shadohead/launchlab-mini/firmware/releases/0.6.0-sticks3-qre1113-rotation/README.md

# Initial single-sensor orientation build

Superseded by 0.6.1. The first VQF rotation-only implementation retained RPM/history and disabled estimated travel, but live feedback exposed missing fused post-roll coverage and a display that erased starting inclination. See `manifest.json`. This is a development checkpoint, not an accepted motion release.
