shadohead/launchlab-mini/firmware/releases/0.6.2-sticks3-qre1113-rotation/source/README.md

# LaunchLab Mini for M5StickS3

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

The current single-sensor orientation recap is saved as
[0.6.2-sticks3-qre1113-rotation](../releases/0.6.2-sticks3-qre1113-rotation/README.md).
The former [estimated-travel recap](../releases/0.5.1-sticks3-qre1113-front/README.md) is preserved.
The prior [cube recap](../releases/0.5.0-sticks3-qre1113-cube/README.md) is preserved.
The prior [frozen level recap](../releases/0.4.3-sticks3-qre1113-recap/README.md) is preserved.
The prior [motion/recreate update](../releases/0.4.2-sticks3-qre1113-feedback/README.md) is preserved.
The prior [power update](../releases/0.3.1-sticks3-qre1113-power/README.md) is preserved.
Version `0.6.2-sticks3-rotation`, for StickS3 K150 (ESP32-S3,
8 MB flash, 8 MB OPI PSRAM). Uses the installed Arduino ESP32 3.3.0,
M5Unified 0.2.23 and M5GFX 0.2.30 dependencies. This is a separate board
application; the Waveshare binary cannot be installed on the M5.

## Acquisition and performance

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

## M5 sensor profile

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

## Wiring and controls

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

## Launch motion and recreate practice

Every accepted pull opens five seconds of feedback: RPM, a fixed-center
launcher rotating in an isometric cube, and frozen Start/End tilt circles.
The launcher stays in one location. There is no travel trail, height estimate,
velocity, displacement, or compass heading. Cube and body size are constant
across captures and have no physical distance units. The replay includes the
recorded 500 ms before and 250 ms after the optical pull, runs once over 1.4
seconds, and holds the last pose. The replay preserves measured gravity-relative tilt. Only arbitrary heading is
reset at optical onset; it does not flatten the initial pose.
The circles record gravity-relative tilt at optical onset/end; they never follow
the current sensor. Recap omits numeric angles and is labeled "Rotation only". The thin portrait
rectangle depicts the sensor board; its white short-edge mark is the USB-C end.
Its neutral heading faces the viewer midway between the two front cube walls,
aligned with the nearest vertical edge, instead of following the left wall.
This fixed 45-degree display-heading offset does not change measured tilt,
relative rotation, or Start/End dots. The rectangle remains centered in the cube.
An unknown board-to-launcher mounting rotation is not silently assumed calibrated.
A recalls the recap; B opens history. RPM acquisition is always enabled.

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

The single IMU owner runs at priority 2 on core 0, below the priority-3 ADC
owner. It shares an I2C mutex with M5 button/power operations and never owns the
ADC. `ORIENTATION_STATUS` reports readiness, bias/uncertainty, rest detection,
resets, update count, and worst fusion duration. Every gap over 35 ms resets
orientation while retaining learned gyro bias; captures overlapping gaps are
rejected. The filter settles for 1.5 seconds after startup/reset. There is no
per-launch hold-still requirement. Naturally occurring rest improves bias.
Clipping near 8 g / 2000 deg/s, missing coverage and optical bursts over 2.5
seconds also make motion unavailable. RPM/history still record independently.
Capture waits for fused-sample post-roll coverage, not the newer raw-poll
timestamp. Saving history waits for the motion post-roll; guarded flash writes can cause
IMU gaps outside the finished capture. Failed saves retain prior durable data.

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

## Practice history

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

## Build and validation

```sh
bash firmware/setup-m5.sh
bash firmware/build-m5.sh
clang++ -std=c++17 -O2 -Ifirmware/LaunchLabRpm firmware/tests/test_sticks3.cpp -o /tmp/test-sticks3
/tmp/test-sticks3
clang++ -std=c++17 -O2 firmware/tests/test_sticks3_level.cpp -o /tmp/test-sticks3-level
/tmp/test-sticks3-level
clang++ -std=c++17 -O1 -g -fsanitize=address,undefined firmware/tests/test_sticks3_power.cpp -o /tmp/test-sticks3-power
/tmp/test-sticks3-power
clang++ -std=c++17 -O1 -g -fsanitize=address,undefined firmware/tests/test_launch_feedback.cpp -o /tmp/test-launch-feedback
/tmp/test-launch-feedback
clang++ -std=c++17 -O1 -g -DVQF_SINGLE_PRECISION -fsanitize=address,undefined firmware/tests/test_orientation_estimator.cpp firmware/LaunchLabMini/src/vqf/vqf.cpp -o /tmp/test-orientation
/tmp/test-orientation
clang++ -std=c++17 -O1 -g -fsanitize=address,undefined firmware/tests/test_motion_replay.cpp -o /tmp/test-motion-replay
/tmp/test-motion-replay
clang++ -std=c++17 -O1 -g -fsanitize=address,undefined firmware/tests/test_launch_motion.cpp -o /tmp/test-launch-motion
/tmp/test-launch-motion
clang++ -std=c++17 -O1 -g -fsanitize=address,undefined -Ifirmware/tests/fakes firmware/tests/test_motion_store.cpp -o /tmp/test-motion-store
/tmp/test-motion-store
clang++ -std=c++17 -O2 -Ifirmware/LaunchLabRpm firmware/tests/replay_sticks3.cpp -o /tmp/replay-sticks3
python3 firmware/tests/check_sticks3_replays.py /tmp/replay-sticks3
clang++ -std=c++17 -O1 -g -fsanitize=address,undefined -Ifirmware/LaunchLabRpm firmware/tests/test_practice_history.cpp -o /tmp/test-practice-history
/tmp/test-practice-history
clang++ -std=c++17 -O1 -g -fsanitize=address,undefined -Ifirmware/tests/fakes firmware/tests/test_practice_store.cpp -o /tmp/test-practice-store
/tmp/test-practice-store
```

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
