shadohead/launchlab-mini/firmware/releases/0.7.0-sticks3-qre1113-singlepeak/source/README.md

# LaunchLab Mini for M5StickS3

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

The current single-sensor orientation recap is saved as
[0.7.0-sticks3-qre1113-singlepeak](../releases/0.7.0-sticks3-qre1113-singlepeak/README.md).
The former [estimated-travel recap](../releases/0.5.1-sticks3-qre1113-front/README.md) is preserved.
The prior [cube recap](../releases/0.5.0-sticks3-qre1113-cube/README.md) is preserved.
The prior [frozen level recap](../releases/0.4.3-sticks3-qre1113-recap/README.md) is preserved.
The prior [motion/recreate update](../releases/0.4.2-sticks3-qre1113-feedback/README.md) is preserved.
The prior [power update](../releases/0.3.1-sticks3-qre1113-power/README.md) is preserved.
Version `0.7.0-sticks3-singlepeak`, for StickS3 K150 (ESP32-S3,
8 MB flash, 8 MB OPI PSRAM). Uses the installed Arduino ESP32 3.3.0,
M5Unified 0.2.23 and M5GFX 0.2.30 dependencies. This is a separate board
application; the Waveshare binary cannot be installed on the M5.

## Acquisition and performance

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

## M5 sensor profile

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

One cycle/revolution, the 1,000-RPM start floor, three consistent revolutions
to confirm a pull, first-burst selection and quiet/rewind rearm remain.
Once a pull is confirmed, **one complete valid revolution can set its peak**.
There is no speed-jump veto or requirement to repeat that faster speed.
Its timing, high/low widths, duty, amplitude and uninterrupted neighboring
mark must agree with established optical shape. The arrival mark is checked
after the 0.5-ms optical mean settles; an oversized mark can otherwise cross
the threshold early and create an artificial short period. This delay needs
no additional full revolution. Sustained three-turn speed continues to govern
slowdown detection, so a brief peak does not end an ongoing pull early.
The shared detector defaults retain the former three-turn peak rule; this
single-turn option is enabled by the current M5 profile only.

The existing timing ceiling is 30,000 RPM (2-ms periods), a measurement bound,
not a scientifically established human limit. Detector edge timestamps have
100-us resolution; a single-turn peak is more sensitive to quantization and
optical jitter than the former average. It remains an average over one turn,
not instantaneous speed within that turn or directly measured release RPM.
`RPM_PEAK_MODE` reports the retained three-turn speed and accepted/rejected
single-peak update counters for diagnosis. No magnetometer/IMU speed estimate
is substituted for optical speed.

The M5 profile reproduces one provisional ~5,128 RPM single-turn result
(~4,945 RPM three-turn speed) in the saved pull and rejects the available
weak idle/handling negatives. Old history retains its original three-turn
values; new records use the single-turn metric. Start a fresh practice session
when switching metrics rather than mixing their averages. It remains an initial
measured profile, not proof of repeatable mounted detection or absolute RPM
accuracy. A different sensor, distance or reflective mark may need a different
profile. Do not remove the amplitude floor or notch 60 Hz: 60 Hz is also a
legitimate 3,600 RPM optical signal.

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

## Wiring and controls

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

## Launch motion and recreate practice

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

## Practice history

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

## Build and validation

```sh
bash firmware/setup-m5.sh
bash firmware/build-m5.sh
clang++ -std=c++17 -O2 -Ifirmware/LaunchLabRpm firmware/tests/test_sticks3.cpp -o /tmp/test-sticks3
/tmp/test-sticks3
clang++ -std=c++17 -O2 firmware/tests/test_sticks3_level.cpp -o /tmp/test-sticks3-level
/tmp/test-sticks3-level
clang++ -std=c++17 -O1 -g -fsanitize=address,undefined firmware/tests/test_sticks3_power.cpp -o /tmp/test-sticks3-power
/tmp/test-sticks3-power
clang++ -std=c++17 -O1 -g -fsanitize=address,undefined firmware/tests/test_launch_feedback.cpp -o /tmp/test-launch-feedback
/tmp/test-launch-feedback
clang++ -std=c++17 -O1 -g -DVQF_SINGLE_PRECISION -fsanitize=address,undefined firmware/tests/test_orientation_estimator.cpp firmware/LaunchLabMini/src/vqf/vqf.cpp -o /tmp/test-orientation
/tmp/test-orientation
clang++ -std=c++17 -O1 -g -fsanitize=address,undefined firmware/tests/test_motion_replay.cpp -o /tmp/test-motion-replay
/tmp/test-motion-replay
clang++ -std=c++17 -O1 -g -fsanitize=address,undefined firmware/tests/test_launch_motion.cpp -o /tmp/test-launch-motion
/tmp/test-launch-motion
clang++ -std=c++17 -O1 -g -fsanitize=address,undefined -Ifirmware/tests/fakes firmware/tests/test_motion_store.cpp -o /tmp/test-motion-store
/tmp/test-motion-store
clang++ -std=c++17 -O2 -Ifirmware/LaunchLabRpm firmware/tests/replay_sticks3.cpp -o /tmp/replay-sticks3
python3 firmware/tests/check_sticks3_replays.py /tmp/replay-sticks3
clang++ -std=c++17 -O1 -g -fsanitize=address,undefined -Ifirmware/LaunchLabRpm firmware/tests/test_practice_history.cpp -o /tmp/test-practice-history
/tmp/test-practice-history
clang++ -std=c++17 -O1 -g -fsanitize=address,undefined -Ifirmware/tests/fakes firmware/tests/test_practice_store.cpp -o /tmp/test-practice-store
/tmp/test-practice-store
```

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
