shadohead/launchlab-mini/firmware/releases/0.3.0-sticks3-qre1113/source/LaunchLabMini/README.md

# Saved QRE1113 Arduino source

This is the self-contained executable source for runtime
`0.3.0-sticks3-practice`, saved as the working M5StickS3 K150 + SparkFun QRE1113
analog package. The sketch and headers match the installed build's source.
See the [package README](../../README.md) for wiring, controls, restoration
and validation, and the [current target documentation](../../../../LaunchLabMini/README.md)
for acquisition and build details.
