shadohead/launchlab-mini/firmware/releases/0.3.1-sticks3-qre1113-power/source/LaunchLabMini/README.md

# Saved Arduino sketch

This is the exact compiled source for runtime `0.3.1-sticks3-power`, saved as
`0.3.1-sticks3-qre1113-power`. See the [release README](../../README.md) for
wiring, controls, restoration and validation.
