shadohead/launchlab-mini/firmware/releases/0.4.3-sticks3-qre1113-recap/source/LaunchLabMini/README.md

# LaunchLab Mini for M5StickS3

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

The current recap update is saved as
[0.4.3-sticks3-qre1113-recap](../releases/0.4.3-sticks3-qre1113-recap/README.md).
The prior [motion/recreate update](../releases/0.4.2-sticks3-qre1113-feedback/README.md) is preserved.
The prior [power update](../releases/0.3.1-sticks3-qre1113-power/README.md) is preserved.
Version `0.4.3-sticks3-recap`, for StickS3 K150 (ESP32-S3,
8 MB flash, 8 MB OPI PSRAM). Uses the installed Arduino ESP32 3.3.0,
M5Unified 0.2.23 and M5GFX 0.2.30 dependencies. This is a separate board
application; the Waveshare binary cannot be installed on the M5.

## Acquisition and performance

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

## M5 sensor profile

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

## Wiring and controls

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

## Launch motion and recreate practice

Every new accepted pull opens five seconds of feedback on the main page,
showing RPM, the same relative turn path, and two frozen circle/dot indicators:
Start on the left and End on the right. These estimate the recorded tilt at
optical burst onset and end, using the pre-launch acceleration baseline and
full-rate gyro integration before the chart is reduced to 48 points. They do
not follow the current live level. The recap omits numeric angles, end rotation
text and the path scale label. Travel height and distance are not estimated.
After capture finishes, the full five-second display starts, then
returns to live automatically. A tap on A recalls the latest launch for another
five seconds; tapping A again returns immediately. Measurement remains enabled
in both views. A newer pull replaces the feedback and restarts the timer.
After reboot, A can show the latest saved RPM; its motion is available only
when that same pull was the saved reference. Otherwise the graph and circles
remain empty until a fresh pull. The most recent in-memory trace is kept after the
five-second display ends. B still opens the history and practice pages.

Tap B from live, then A through the tabs to Motion or Recreate. There is no
hold-still requirement; capture runs during normal handling and pulls. Motion draws the launcher's relative tilt
path in degrees. The first usable pull in Recreate becomes the reference;
subsequent pulls compare against it. Hold A to select the latest usable pull,
or hold B to use the next usable pull as a new reference. The reference is
saved across reboot in separate alternating checksummed `ll-motion` NVS slots.
Schema 3 stores both frozen tilt snapshots and the automatic stationary-bias
flag in the existing 1124-byte image. Schema-1 and schema-2 references remain
readable; their start/end tilt is reconstructed from their recorded gyro and
baseline data.
No historical motion is invented for earlier RPM-only records. The latest
attempt stays in RAM; this version retains one reference, not every motion trace.

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

## Practice history

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

## Build and validation

```sh
bash firmware/setup-m5.sh
bash firmware/build-m5.sh
clang++ -std=c++17 -O2 -Ifirmware/LaunchLabRpm firmware/tests/test_sticks3.cpp -o /tmp/test-sticks3
/tmp/test-sticks3
clang++ -std=c++17 -O2 firmware/tests/test_sticks3_level.cpp -o /tmp/test-sticks3-level
/tmp/test-sticks3-level
clang++ -std=c++17 -O1 -g -fsanitize=address,undefined firmware/tests/test_sticks3_power.cpp -o /tmp/test-sticks3-power
/tmp/test-sticks3-power
clang++ -std=c++17 -O1 -g -fsanitize=address,undefined firmware/tests/test_launch_feedback.cpp -o /tmp/test-launch-feedback
/tmp/test-launch-feedback
clang++ -std=c++17 -O1 -g -fsanitize=address,undefined firmware/tests/test_launch_motion.cpp -o /tmp/test-launch-motion
/tmp/test-launch-motion
clang++ -std=c++17 -O1 -g -fsanitize=address,undefined -Ifirmware/tests/fakes firmware/tests/test_motion_store.cpp -o /tmp/test-motion-store
/tmp/test-motion-store
clang++ -std=c++17 -O2 -Ifirmware/LaunchLabRpm firmware/tests/replay_sticks3.cpp -o /tmp/replay-sticks3
python3 firmware/tests/check_sticks3_replays.py /tmp/replay-sticks3
clang++ -std=c++17 -O1 -g -fsanitize=address,undefined -Ifirmware/LaunchLabRpm firmware/tests/test_practice_history.cpp -o /tmp/test-practice-history
/tmp/test-practice-history
clang++ -std=c++17 -O1 -g -fsanitize=address,undefined -Ifirmware/tests/fakes firmware/tests/test_practice_store.cpp -o /tmp/test-practice-store
/tmp/test-practice-store
```

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
