shadohead/launchlab-mini/firmware/releases/0.5.0-sticks3-qre1113-cube/source/LaunchLabMini/README.md

# LaunchLab Mini for M5StickS3

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

The current 3D cube recap is saved as
[0.5.0-sticks3-qre1113-cube](../releases/0.5.0-sticks3-qre1113-cube/README.md).
The prior [frozen level recap](../releases/0.4.3-sticks3-qre1113-recap/README.md) is preserved.
The prior [motion/recreate update](../releases/0.4.2-sticks3-qre1113-feedback/README.md) is preserved.
The prior [power update](../releases/0.3.1-sticks3-qre1113-power/README.md) is preserved.
Version `0.5.0-sticks3-cube`, for StickS3 K150 (ESP32-S3,
8 MB flash, 8 MB OPI PSRAM). Uses the installed Arduino ESP32 3.3.0,
M5Unified 0.2.23 and M5GFX 0.2.30 dependencies. This is a separate board
application; the Waveshare binary cannot be installed on the M5.

## Acquisition and performance

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

## M5 sensor profile

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

## Wiring and controls

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

## Launch motion and recreate practice

Every new accepted pull opens five seconds of feedback on the main page,
showing RPM, an isometric cube replay, and two frozen circle/dot indicators:
Start on the left and End on the right. These estimate the recorded tilt at
optical burst onset and end, using the pre-launch acceleration baseline and
full-rate gyro integration before the chart is reduced to 48 points. They do
not follow the current live level. The recap omits numeric angles and end rotation
text. A rectangular launcher rotates from recorded gyro orientation and moves
along an **estimated** short-window travel trail. The replay runs once over
1.4 seconds, then holds its final pose for the rest of the recap. The cube has
equal sides, encloses the full trace and glyph, and centers zero starting height
so rises and dips remain visible. A ring on the right face facing the viewer
marks the start and connects to the true zero-origin pose inside the cube.
Gray shows the reference/end pose and cyan shows the latest attempt.

`motion_replay.h` integrates the stored acceleration change only from optical
onset to optical end, interpolating by elapsed time. Gravity defines the up
axis, and the device's screen-top direction at onset defines horizontal forward.
The glyph starts facing the viewer; its subsequent rotation is relative to onset.
The starting velocity is unknown and assumed zero. Pre-launch acceleration,
gyro bias, mounting orientation and integration drift can distort this trail,
especially with a moving baseline. This is an experimental relative visual,
not calibrated height, distance or a measured Beyblade trajectory. No numeric
distance or height is displayed and no hold-still requirement is added.
After capture finishes, the full five-second display starts, then
returns to live automatically. A tap on A recalls the latest launch for another
five seconds; tapping A again returns immediately. Measurement remains enabled
in both views. A newer pull replaces the feedback and restarts the timer.
After reboot, A can show the latest saved RPM; its motion is available only
when that same pull was the saved reference. Otherwise the graph and circles
remain empty until a fresh pull. The most recent in-memory trace is kept after the
five-second display ends. B still opens the history and practice pages.

Tap B from live, then A through the tabs to Motion or Recreate. There is no
hold-still requirement; capture runs during normal handling and pulls. Motion shows
the same isometric cube at the final pose. The first usable pull in Recreate becomes the reference;
subsequent pulls compare against it. Hold A to select the latest usable pull,
or hold B to use the next usable pull as a new reference. The reference is
saved across reboot in separate alternating checksummed `ll-motion` NVS slots.
Schema 3 stores both frozen tilt snapshots and the automatic stationary-bias
flag in the existing 1124-byte image. Schema-1 and schema-2 references remain
readable; their start/end tilt is reconstructed from their recorded gyro and
baseline data.
No historical motion is invented for earlier RPM-only records. The latest
attempt stays in RAM; this version retains one reference, not every motion trace.

Gray is the reference; cyan is the latest attempt. Recreate displays actual
peak RPM and its signed difference/percentage, a full 3D relative-rotation RMS
error in degrees, acceleration-change and angular-speed overlays, acceleration
RMS error and pull-duration difference. Each overlay shares the same scale and
elapsed time, with zero at optical burst onset. Comparisons interpolate the
reference over shared time without stretching either pull to match duration.
Errors use all three axes, even though the two graphs show vector magnitudes.
The cube glyph includes all three relative rotation axes, including twist;
Recreate uses the same full quaternion when calculating rotation error.

Fresh paired acceleration/gyro samples come from one dedicated IMU owner
on core 0 at priority 2, below the priority-3 optical ADC owner.
M5 button/power/battery operations share its I2C mutex. UI drawing and USB
stalls on core 1 do not own the task. Flash/cache stalls can still produce
counted gaps; captures overlapping them are rejected. A 1024-sample ring keeps
pre-launch data; captures
cover 500 ms before optical onset to 250 ms after burst end, reduced to at most
48 points with their actual timestamps. A 250-ms baseline ending 600 ms before
onset provides the
pre-launch acceleration vector. Only a naturally stable baseline estimates gyro
bias; a moving baseline uses the SDK gyro values directly and is accepted.
Gyro integration produces relative orientation. Acceleration change is the
rotated measured vector minus that pre-launch baseline, not guaranteed isolated
linear acceleration when the baseline itself was moving. This measures relative
turns and acceleration. The cube derives an experimental displacement estimate
from those recorded vectors; absolute spatial position is unavailable.
Optical/IMU clock alignment is approximate at the
DMA-frame and polling resolution, rather than hardware synchronized.

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

## Practice history

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

## Build and validation

```sh
bash firmware/setup-m5.sh
bash firmware/build-m5.sh
clang++ -std=c++17 -O2 -Ifirmware/LaunchLabRpm firmware/tests/test_sticks3.cpp -o /tmp/test-sticks3
/tmp/test-sticks3
clang++ -std=c++17 -O2 firmware/tests/test_sticks3_level.cpp -o /tmp/test-sticks3-level
/tmp/test-sticks3-level
clang++ -std=c++17 -O1 -g -fsanitize=address,undefined firmware/tests/test_sticks3_power.cpp -o /tmp/test-sticks3-power
/tmp/test-sticks3-power
clang++ -std=c++17 -O1 -g -fsanitize=address,undefined firmware/tests/test_launch_feedback.cpp -o /tmp/test-launch-feedback
/tmp/test-launch-feedback
clang++ -std=c++17 -O1 -g -fsanitize=address,undefined firmware/tests/test_launch_motion.cpp -o /tmp/test-launch-motion
/tmp/test-launch-motion
clang++ -std=c++17 -O1 -g -fsanitize=address,undefined -Ifirmware/tests/fakes firmware/tests/test_motion_store.cpp -o /tmp/test-motion-store
/tmp/test-motion-store
clang++ -std=c++17 -O2 -Ifirmware/LaunchLabRpm firmware/tests/replay_sticks3.cpp -o /tmp/replay-sticks3
python3 firmware/tests/check_sticks3_replays.py /tmp/replay-sticks3
clang++ -std=c++17 -O1 -g -fsanitize=address,undefined -Ifirmware/LaunchLabRpm firmware/tests/test_practice_history.cpp -o /tmp/test-practice-history
/tmp/test-practice-history
clang++ -std=c++17 -O1 -g -fsanitize=address,undefined -Ifirmware/tests/fakes firmware/tests/test_practice_store.cpp -o /tmp/test-practice-store
/tmp/test-practice-store
```

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
