shadohead/launchlab-mini/firmware/releases/0.10.1-sticks3-qre1113-tiltreplay/evidence/tilt-replay.gif

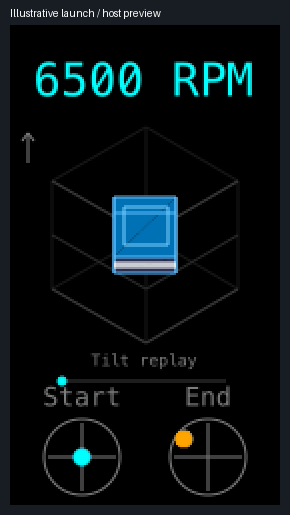
firmware/releases/0.10.1-sticks3-qre1113-tiltreplay/evidence/tilt-replay.gif
