shadohead/launchlab-mini/hardware/LaunchLab_v019_tcrt5000_open_stack/references/IMG_7447.jpeg

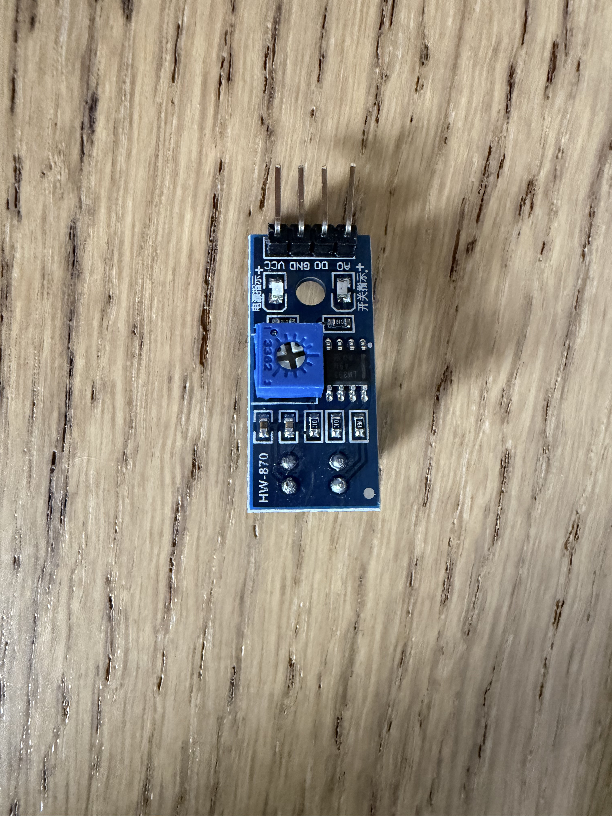
hardware/LaunchLab_v019_tcrt5000_open_stack/references/IMG_7447.jpeg
