shadohead/launchlab-mini/hardware/LaunchLab_v019_tcrt5000_open_stack/references/IMG_7448.jpeg

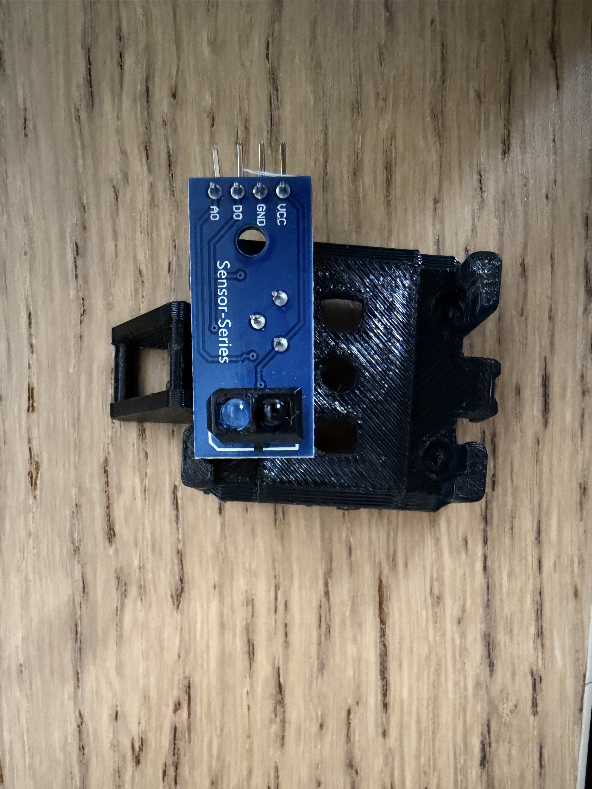
hardware/LaunchLab_v019_tcrt5000_open_stack/references/IMG_7448.jpeg
