shadohead/launchlab-mini/hardware/LaunchLab_v019_tcrt5000_open_stack/renders/02_underside_sensor.png

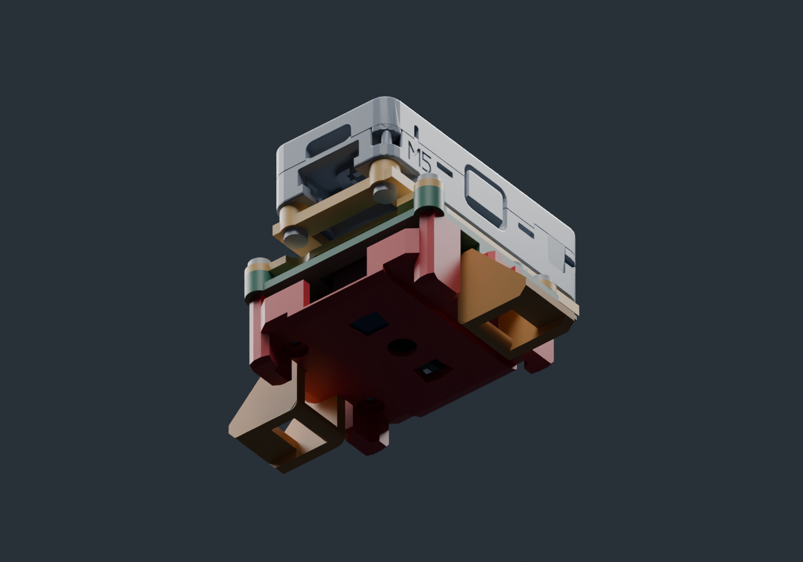
hardware/LaunchLab_v019_tcrt5000_open_stack/renders/02_underside_sensor.png
