shadohead/launchlab-mini/hardware/LaunchLab_v019_tcrt5000_open_stack/renders/03_exploded.png

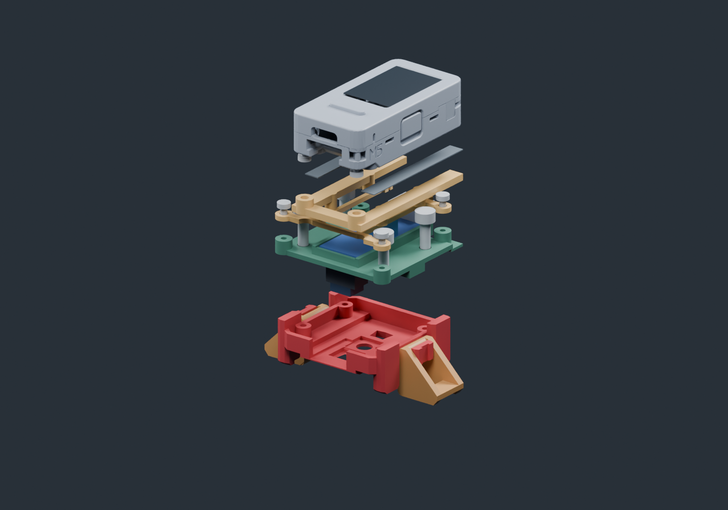
hardware/LaunchLab_v019_tcrt5000_open_stack/renders/03_exploded.png
