shadohead/launchlab-mini/hardware/LaunchLab_v019_tcrt5000_open_stack/renders/04_complete_five_pieces.png

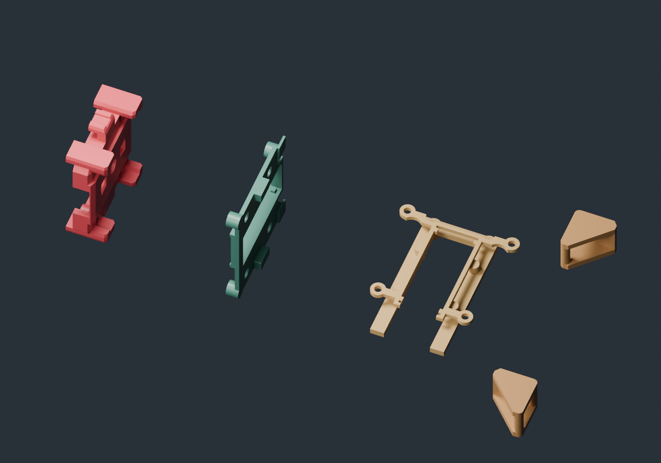
hardware/LaunchLab_v019_tcrt5000_open_stack/renders/04_complete_five_pieces.png
