shadohead/launchlab-mini/hardware/LaunchLab_v033_flush_QRE/references/IMG_7549_preview.png

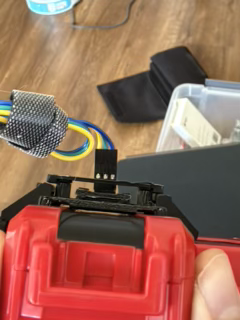
hardware/LaunchLab_v033_flush_QRE/references/IMG_7549_preview.png
