shadohead/launchlab-mini/hardware/LaunchLab_v040_ALL_ITEMS_PRINT/reports/M5_before_after.png

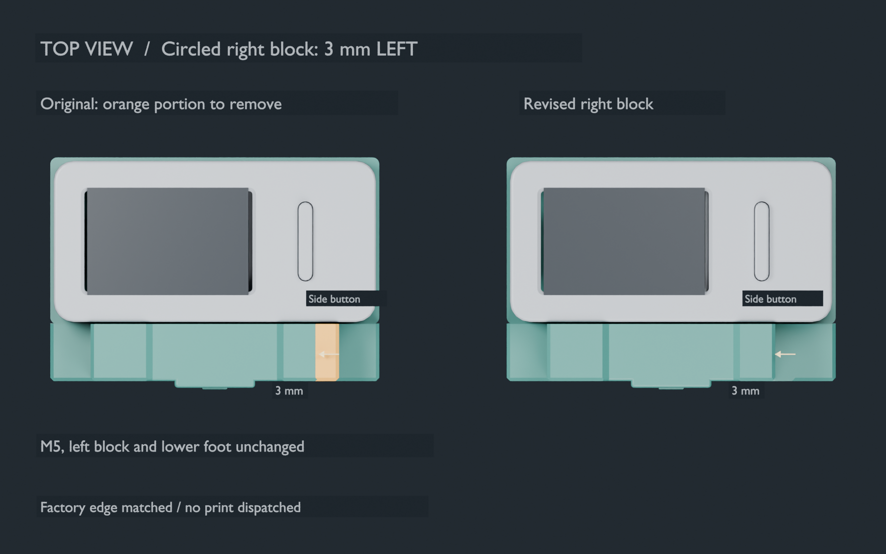
hardware/LaunchLab_v040_ALL_ITEMS_PRINT/reports/M5_before_after.png
