shadohead/launchlab-mini/hardware/M5_cable_hook_v068/renders/03_hook_opening.png

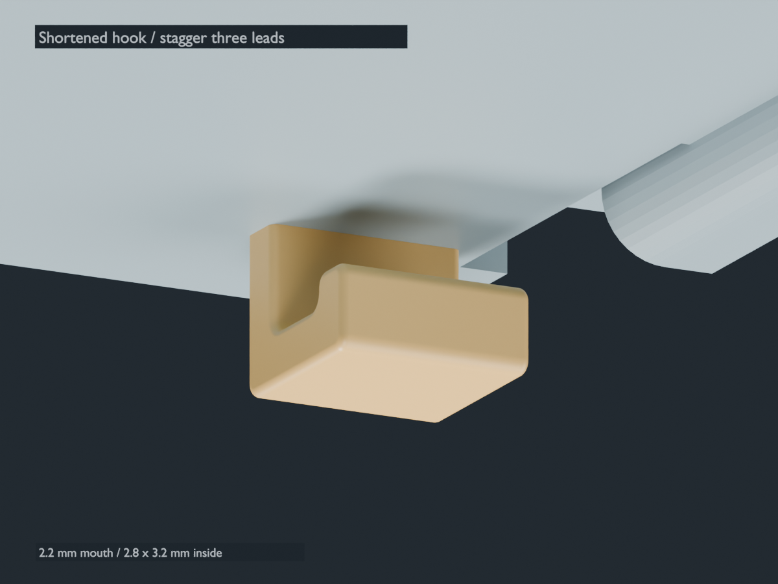
hardware/M5_cable_hook_v068/renders/03_hook_opening.png
