shadohead/launchlab-mini/hardware/M5_cable_hook_v068/reports/plate_1.png

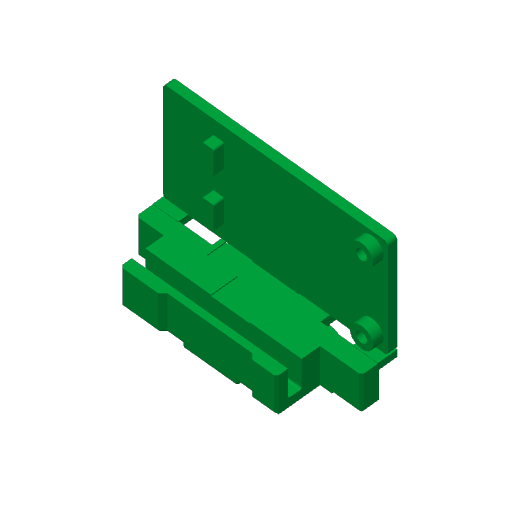
hardware/M5_cable_hook_v068/reports/plate_1.png
