shadohead/launchlab-mini/hardware/M5_equal_supports_v050/references/USER_center_rectangle.png

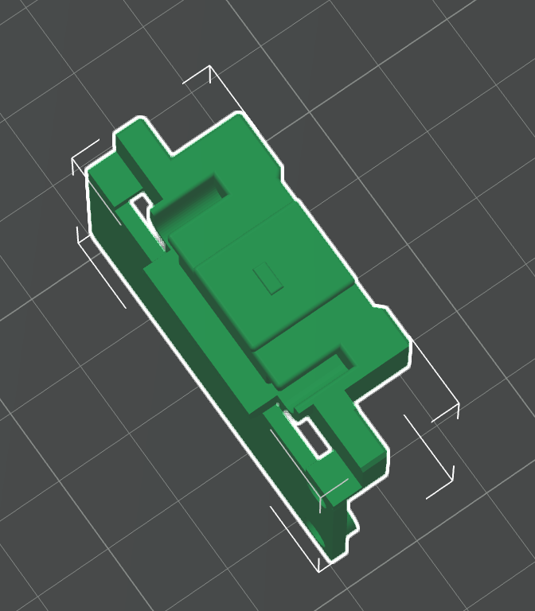
hardware/M5_equal_supports_v050/references/USER_center_rectangle.png
