shadohead/launchlab-mini/hardware/M5_equal_supports_v050/renders/01_raised_supports.png

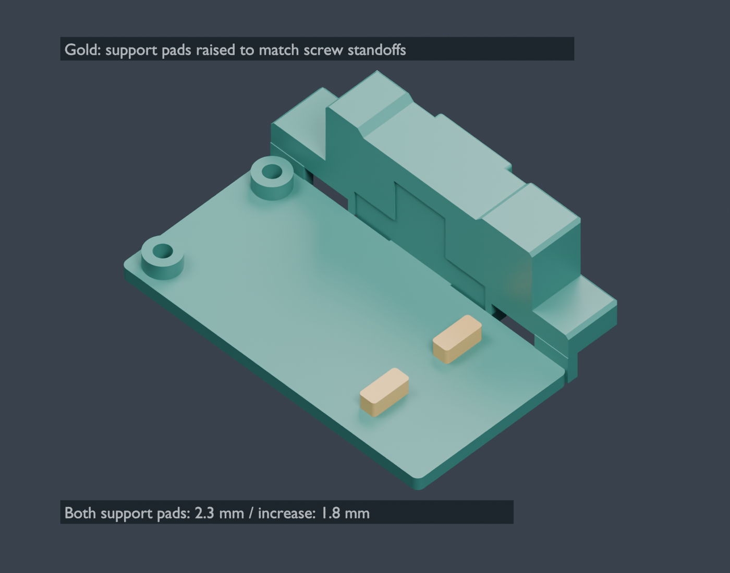
hardware/M5_equal_supports_v050/renders/01_raised_supports.png
