shadohead/launchlab-mini/hardware/M5_equal_supports_v050/renders/02_height_alignment.png

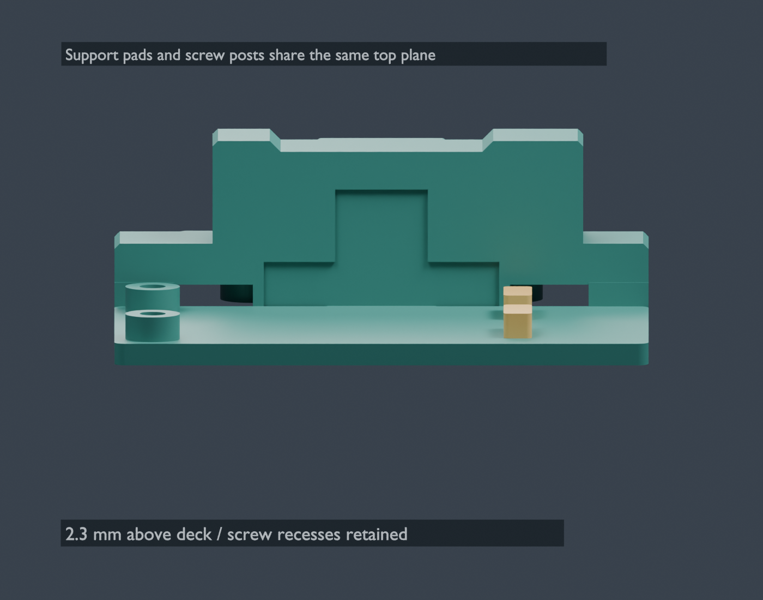
hardware/M5_equal_supports_v050/renders/02_height_alignment.png
