shadohead/launchlab-mini/hardware/M5_equal_supports_v050/renders/03_support_closeup.png

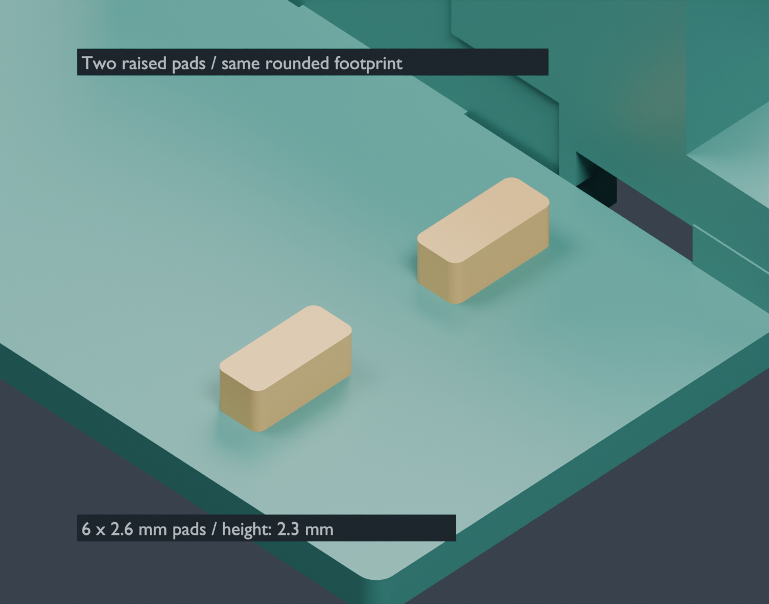
hardware/M5_equal_supports_v050/renders/03_support_closeup.png
