shadohead/launchlab-mini/hardware/M5_level_support_v044/references/USER_M5_level_markup.png

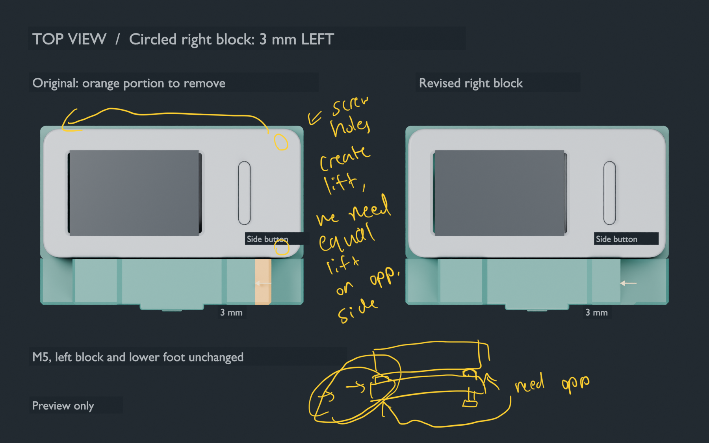
hardware/M5_level_support_v044/references/USER_M5_level_markup.png
