shadohead/launchlab-mini/hardware/M5_level_support_v044/renders/03_exploded.png

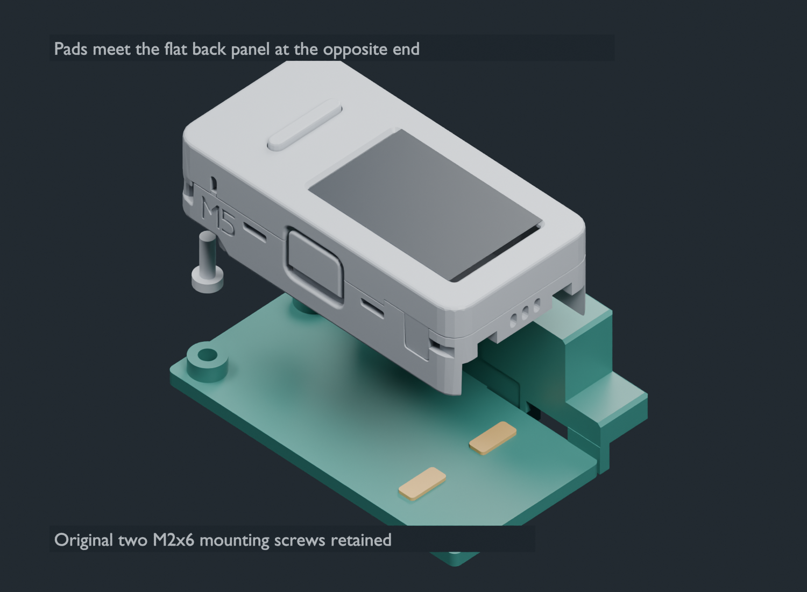
hardware/M5_level_support_v044/renders/03_exploded.png
