shadohead/launchlab-mini/hardware/M5_level_support_v044/renders/04_side_contact.png

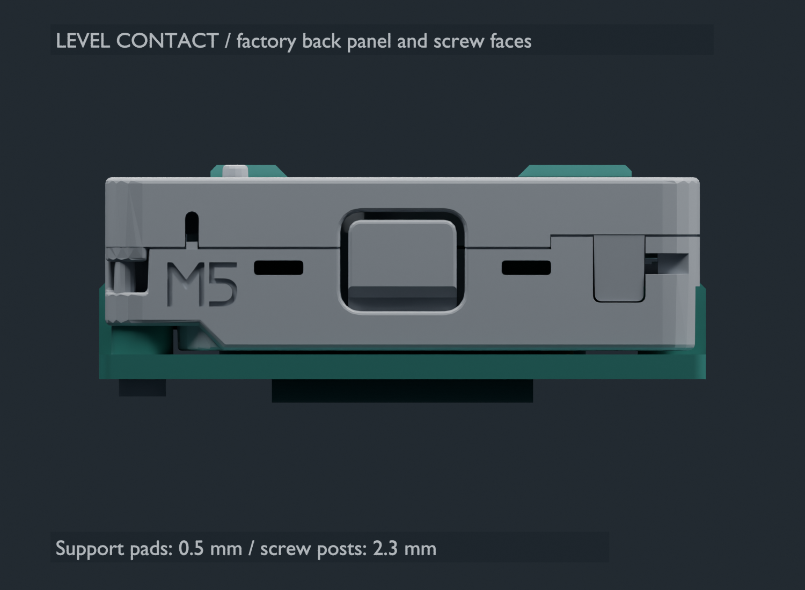
hardware/M5_level_support_v044/renders/04_side_contact.png
