shadohead/launchlab-mini/hardware/M5_raised_rectangle_v046/renders/01_revised_carrier.png

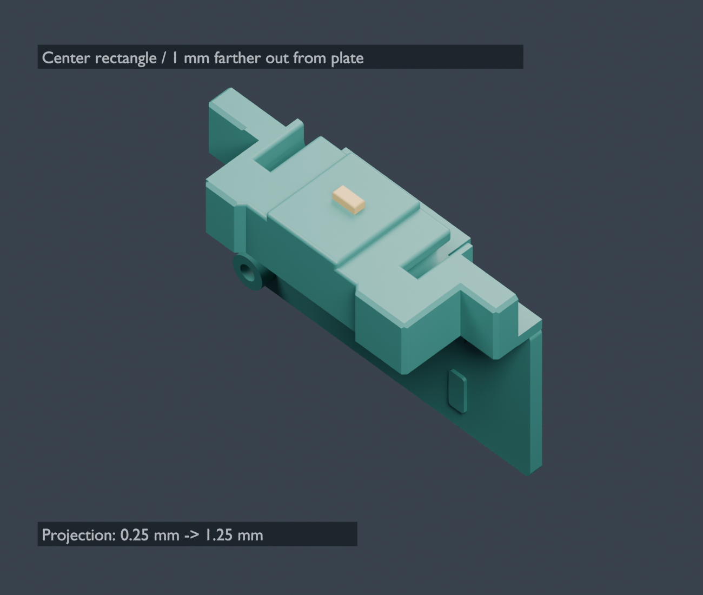
hardware/M5_raised_rectangle_v046/renders/01_revised_carrier.png
