shadohead/launchlab-mini/hardware/M5_raised_rectangle_v046/renders/02_revised_closeup.png

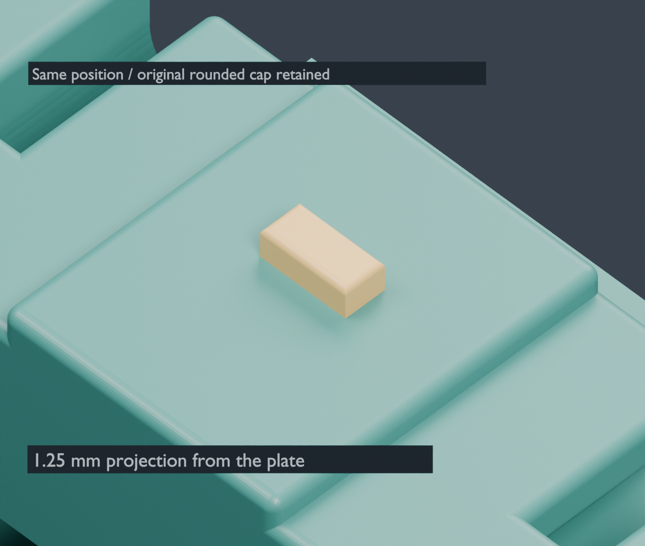
hardware/M5_raised_rectangle_v046/renders/02_revised_closeup.png
