shadohead/launchlab-mini/hardware/M5_raised_rectangle_v046/renders/03_original_closeup.png

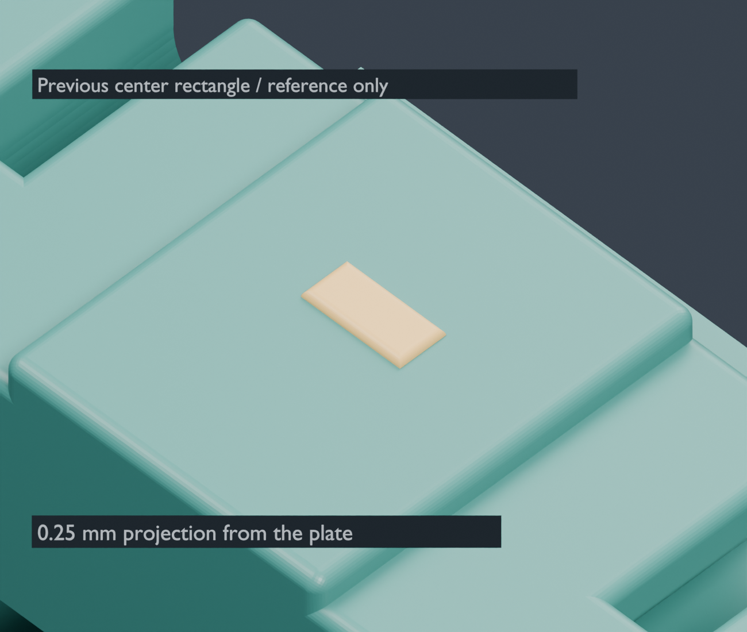
hardware/M5_raised_rectangle_v046/renders/03_original_closeup.png
