shadohead/launchlab-mini/hardware/M5_raised_rectangle_v046/renders/04_center_section.png

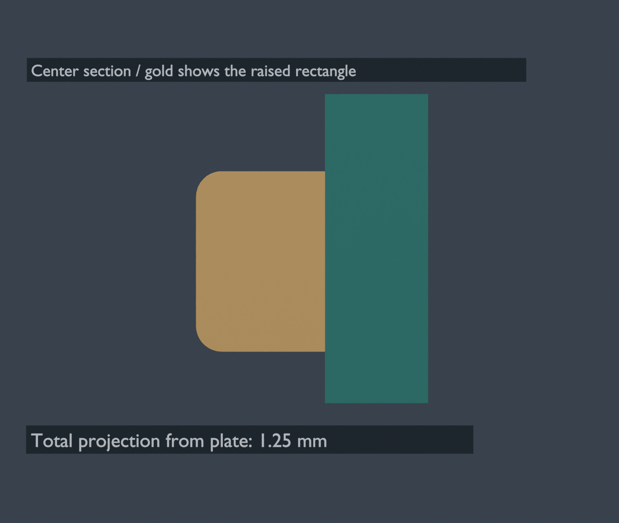
hardware/M5_raised_rectangle_v046/renders/04_center_section.png
