shadohead/launchlab-mini/hardware/M5_recessed_screws_v045/renders/03_axial_section.png

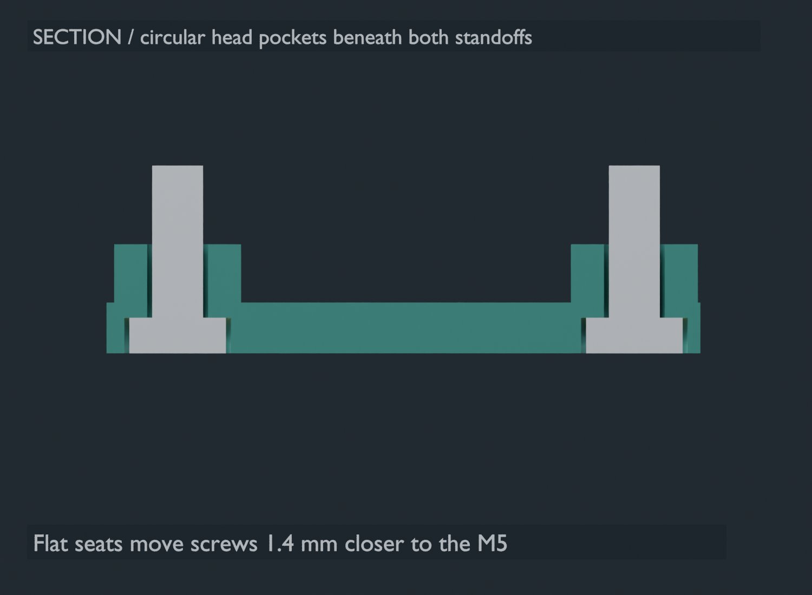
hardware/M5_recessed_screws_v045/renders/03_axial_section.png
