shadohead/launchlab-mini/hardware/M5_recessed_screws_v045/renders/04_top_unchanged.png

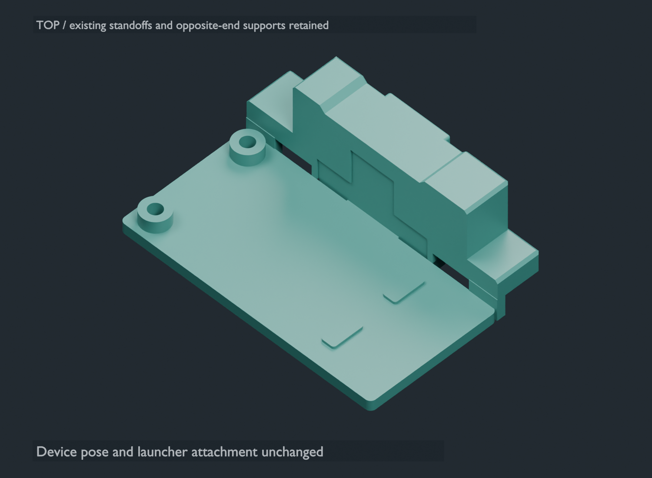
hardware/M5_recessed_screws_v045/renders/04_top_unchanged.png
