shadohead/launchlab-mini/hardware/M5_rotated_rectangle_v047/renders/01_revised_carrier.png

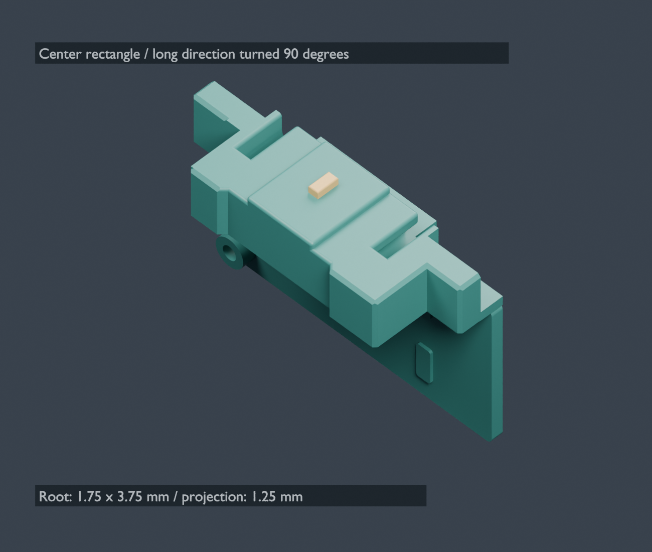
hardware/M5_rotated_rectangle_v047/renders/01_revised_carrier.png
