shadohead/launchlab-mini/hardware/M5_rotated_rectangle_v047/renders/02_revised_closeup.png

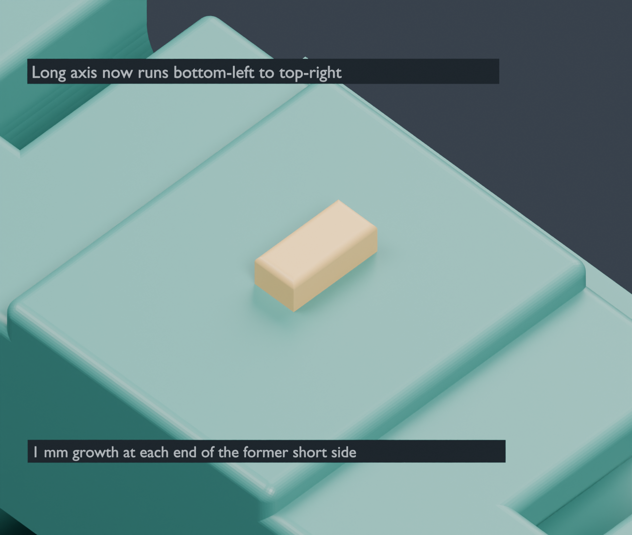
hardware/M5_rotated_rectangle_v047/renders/02_revised_closeup.png
