shadohead/launchlab-mini/hardware/M5_rotated_rectangle_v047/renders/04_footprint_top.png

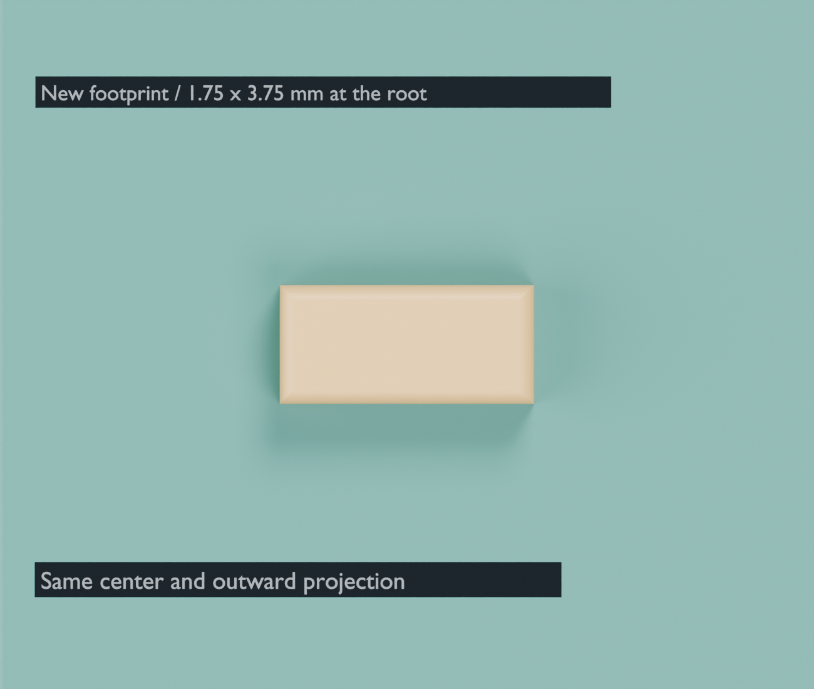
hardware/M5_rotated_rectangle_v047/renders/04_footprint_top.png
