shadohead/launchlab-mini/hardware/M5_smooth_rectangle_v048/renders/01_revised_carrier.png

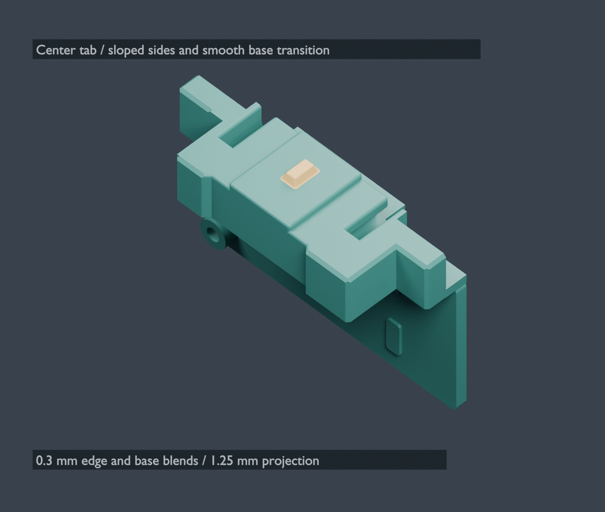
hardware/M5_smooth_rectangle_v048/renders/01_revised_carrier.png
