shadohead/launchlab-mini/hardware/M5_smooth_rectangle_v048/renders/02_revised_closeup.png

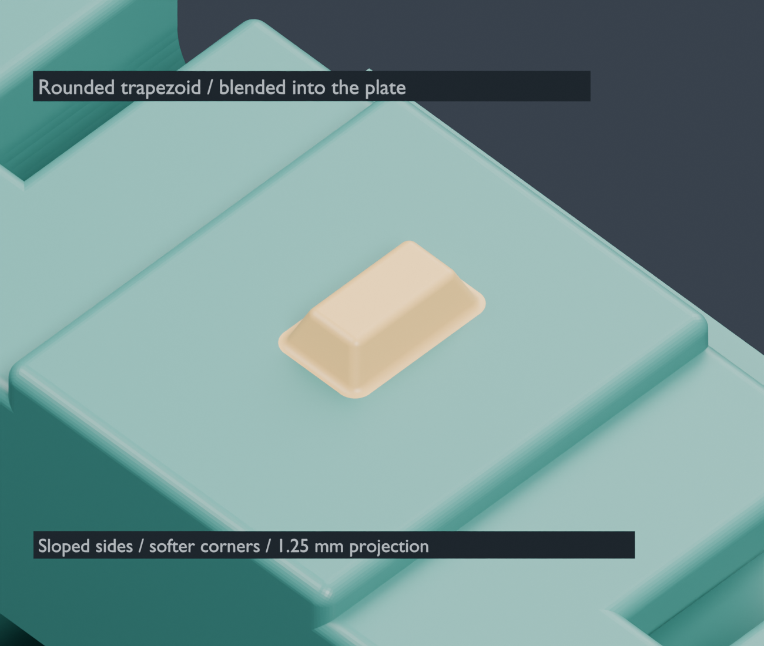
hardware/M5_smooth_rectangle_v048/renders/02_revised_closeup.png
