shadohead/launchlab-mini/hardware/M5_smooth_rectangle_v048/renders/04_footprint_top.png

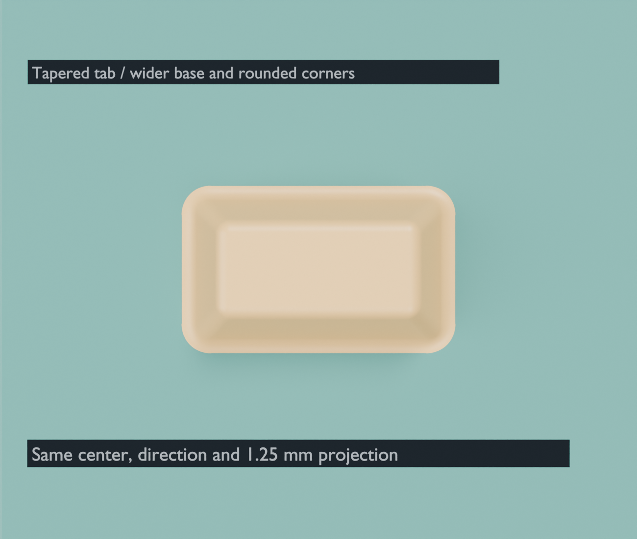
hardware/M5_smooth_rectangle_v048/renders/04_footprint_top.png
