shadohead/launchlab-mini/hardware/M5_soft_ramp_v049/renders/04_footprint_top.png

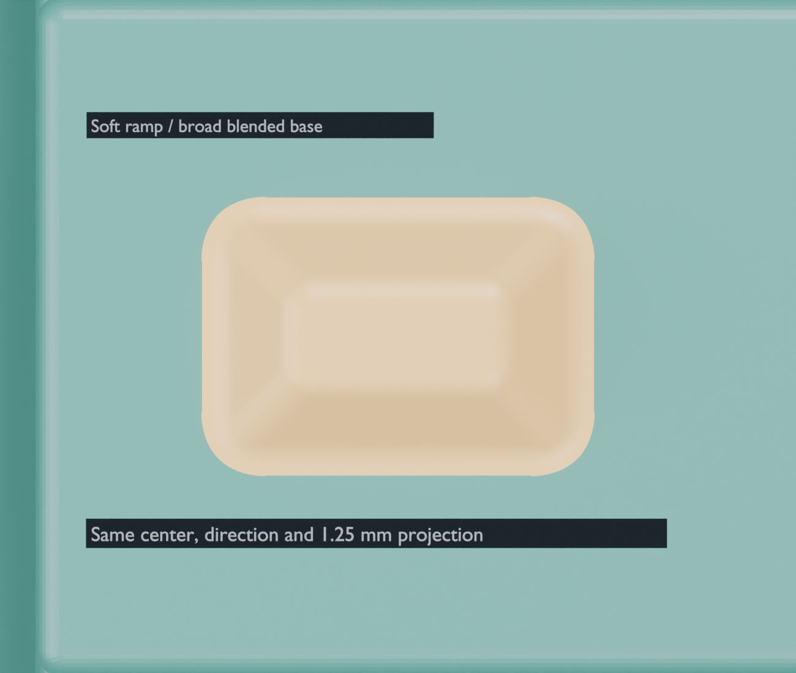
hardware/M5_soft_ramp_v049/renders/04_footprint_top.png
