shadohead/launchlab-mini/hardware/minimal_TCRT_sensor_only_v042/renders/02_sensor_cradle.png

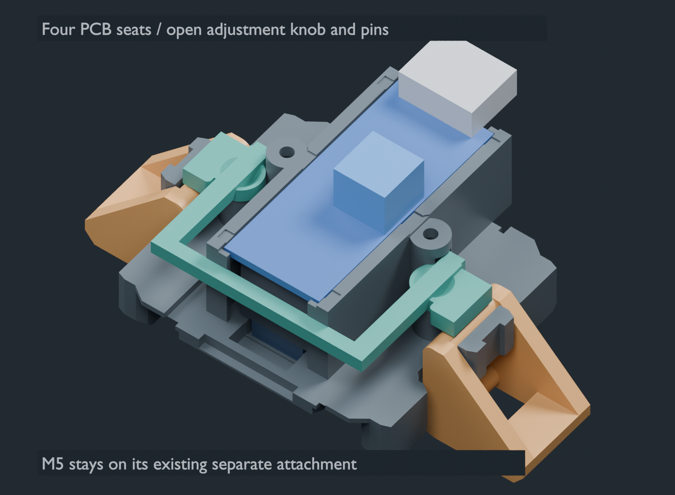
hardware/minimal_TCRT_sensor_only_v042/renders/02_sensor_cradle.png
