shadohead/launchlab-mini/hardware/minimal_TCRT_sensor_only_v042/renders/03_exploded.png

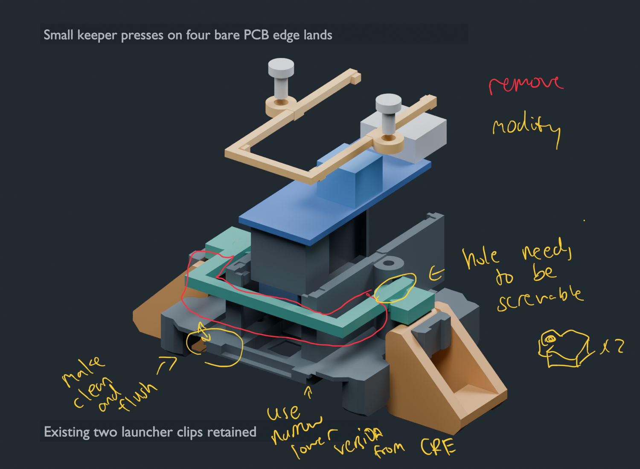
hardware/minimal_TCRT_sensor_only_v042/renders/03_exploded.png
