shadohead/launchlab-mini/hardware/minimal_TCRT_sensor_only_v042/renders/04_underside.png

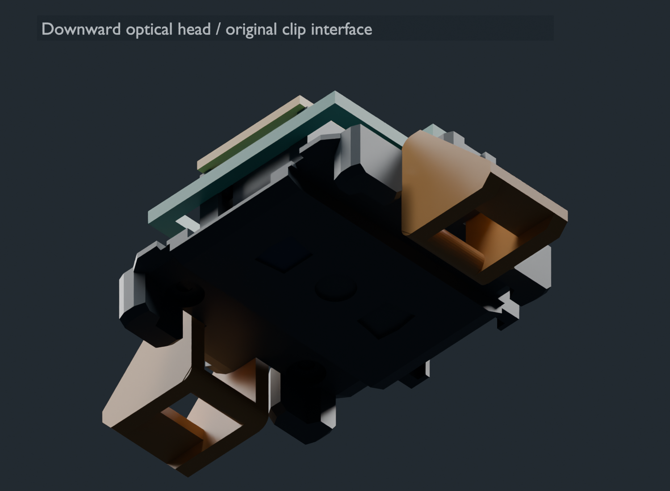
hardware/minimal_TCRT_sensor_only_v042/renders/04_underside.png
