shadohead/launchlab-mini/hardware/minimal_TCRT_split_keepers_v043/renders/02_sensor_cradle.png

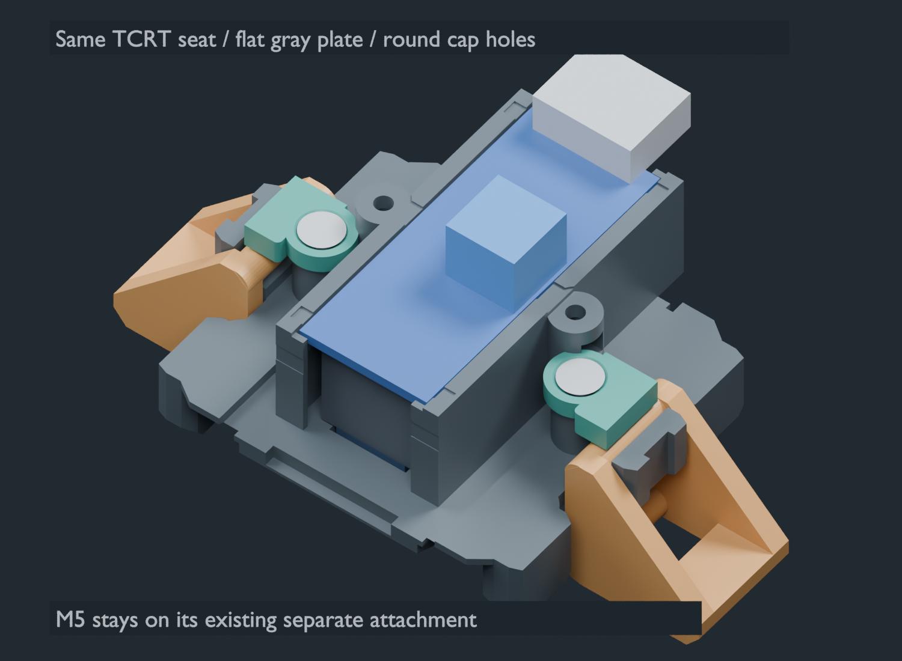
hardware/minimal_TCRT_split_keepers_v043/renders/02_sensor_cradle.png
