shadohead/launchlab-mini/hardware/minimal_TCRT_stack_v041/renders/03_exploded.png

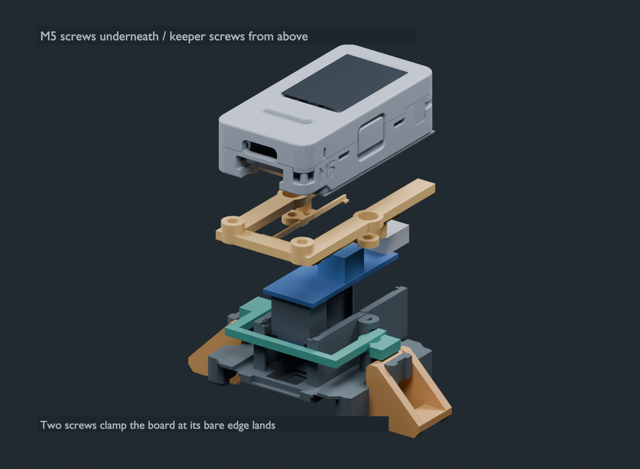
hardware/minimal_TCRT_stack_v041/renders/03_exploded.png
