shadohead/launchlab-mini/hardware/LaunchLab_v040_ALL_ITEMS_PRINT/stl/01_M5_stepped_platform.stl

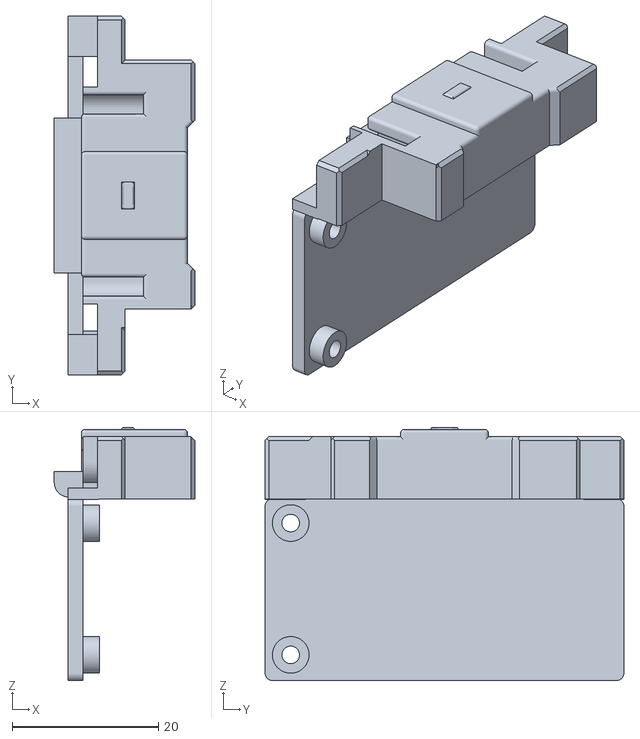
[picture p90: CAD file, 2026-10-02]
hardware/LaunchLab_v040_ALL_ITEMS_PRINT/stl/01_M5_stepped_platform.stl
19.2 x 49.0 x 34.5
