shadohead/launchlab-mini/hardware/LaunchLab_v040_right_block_print/references/REMOVED_circled_right_3mm_visual.stl

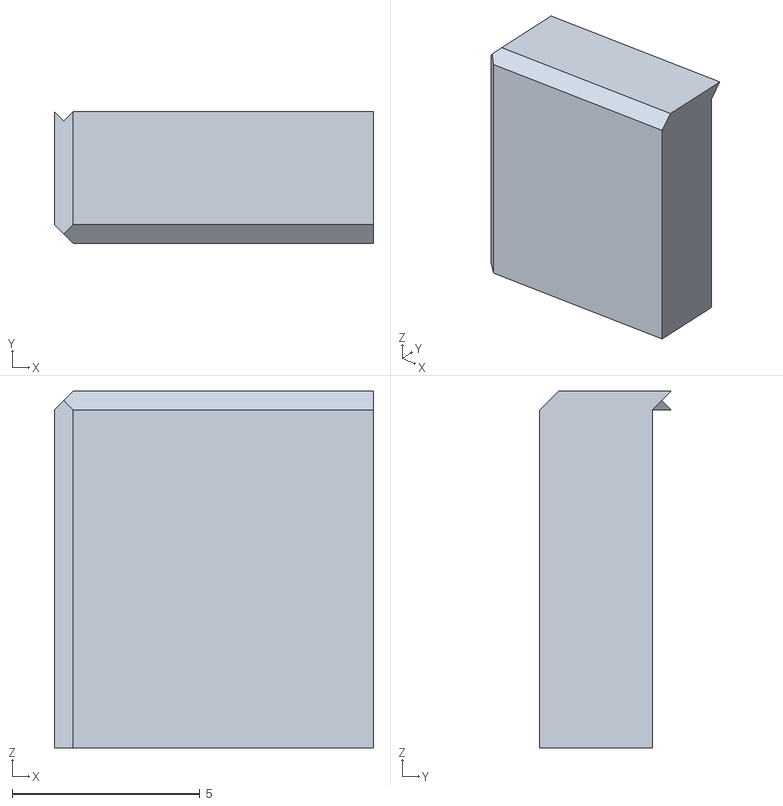
[picture p91: CAD file, 2026-10-02]
hardware/LaunchLab_v040_right_block_print/references/REMOVED_circled_right_3mm_visual.stl
8.50 x 3.50 x 9.50
