shadohead/launchlab-mini/hardware/M5_cable_hook_v068/bambu/LaunchLab_v068_P1S_PLA_M5_ATTACHMENT_PROTOTYPE.3mf

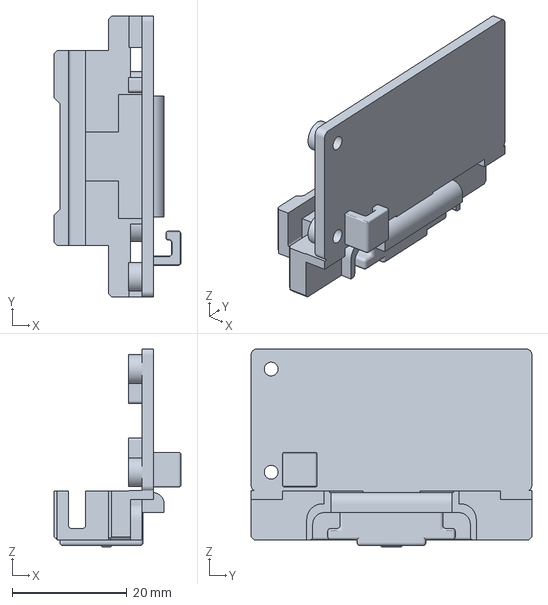
[picture p92: CAD file, 2026-10-05]
hardware/M5_cable_hook_v068/bambu/LaunchLab_v068_P1S_PLA_M5_ATTACHMENT_PROTOTYPE.3mf
22.1 x 49.0 x 34.5 mm
