shadohead/launchlab-mini/hardware/M5_cable_hook_v068/references/SLICER_SUPPORT_BLOCKER_ONLY.stl

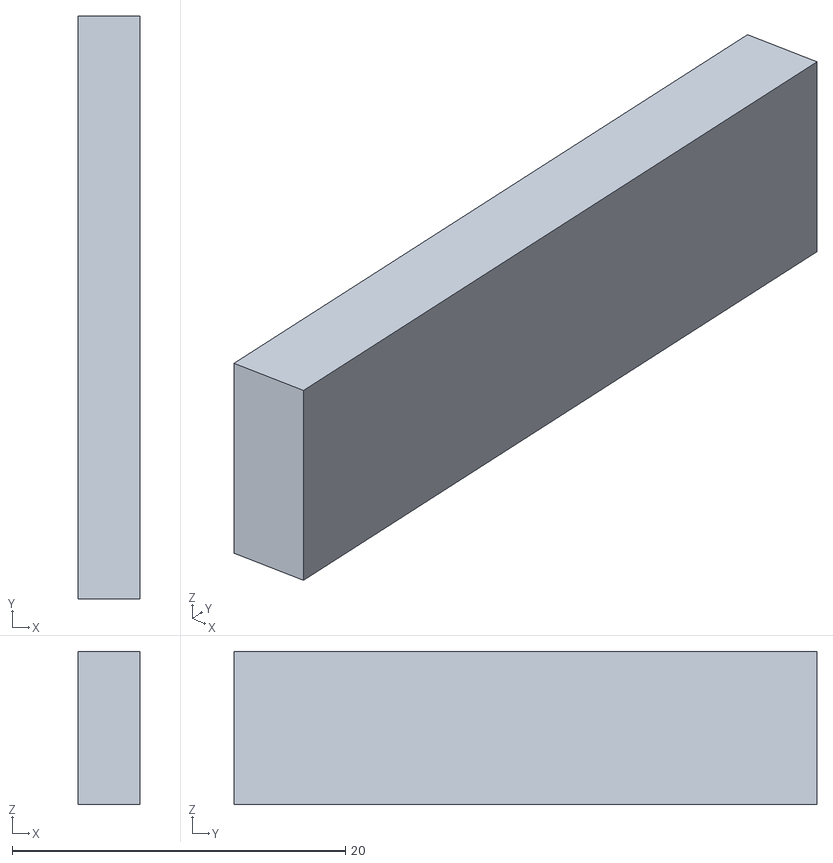
[picture p93: CAD file, 2026-10-05]
hardware/M5_cable_hook_v068/references/SLICER_SUPPORT_BLOCKER_ONLY.stl
3.70 x 35.0 x 9.20
