shadohead/launchlab-mini/hardware/M5_cable_hook_v068/source/carrier_before_hook.stl

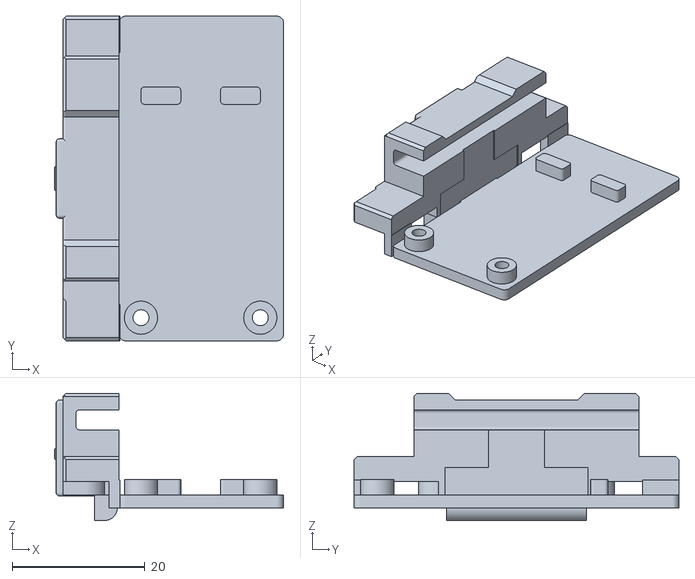
[picture p94: CAD file, 2026-10-05]
hardware/M5_cable_hook_v068/source/carrier_before_hook.stl
34.5 x 49.0 x 19.2
