shadohead/launchlab-mini/hardware/M5_cable_hook_v068/step/CABLE_HOOK_ONLY.step

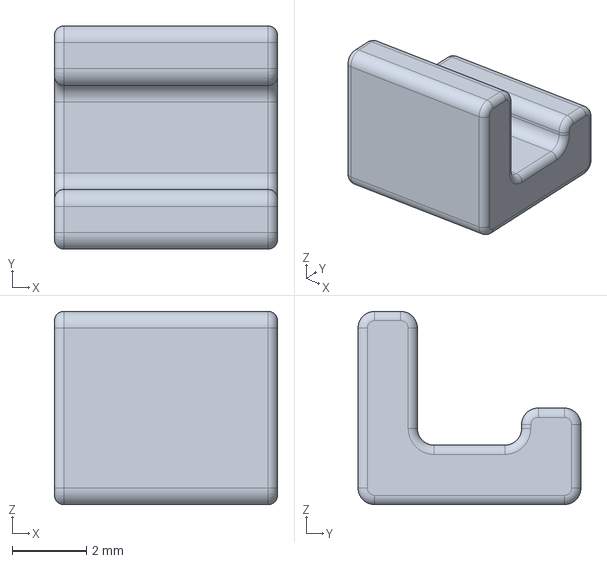
[picture p95: CAD file, 2026-10-05]
hardware/M5_cable_hook_v068/step/CABLE_HOOK_ONLY.step
6.00 x 6.00 x 5.20 mm
