shadohead/launchlab-mini/hardware/M5_equal_supports_v050/bambu/LaunchLab_v050_P1S_PLA_M5_EQUAL_SUPPORTS_TREE_SLIM.3mf

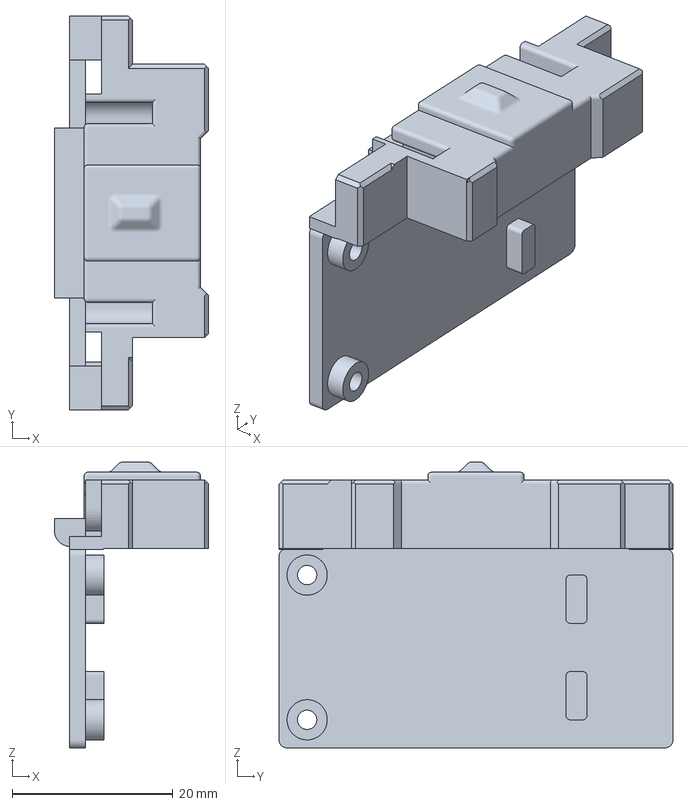
[picture p96: CAD file, 2026-10-03]
hardware/M5_equal_supports_v050/bambu/LaunchLab_v050_P1S_PLA_M5_EQUAL_SUPPORTS_TREE_SLIM.3mf
19.2 x 49.0 x 35.5 mm
