shadohead/launchlab-mini/hardware/M5_equal_supports_v050/references/Equal_height_support_1.stl

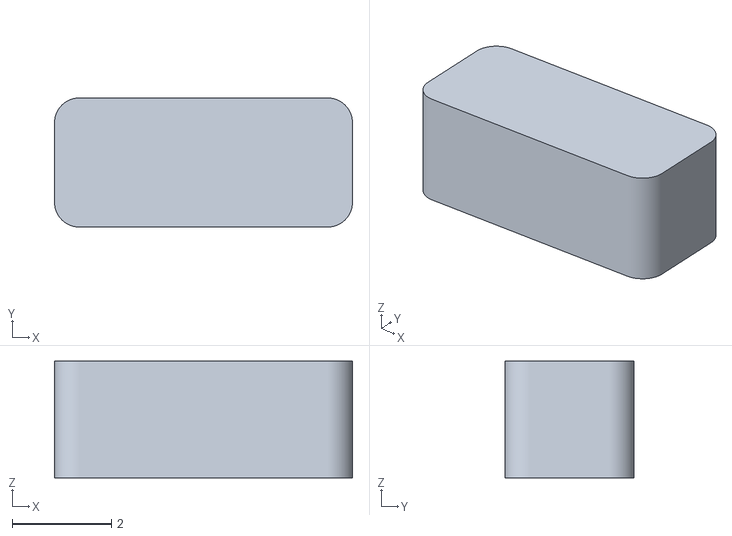
[picture p97: CAD file, 2026-10-03]
hardware/M5_equal_supports_v050/references/Equal_height_support_1.stl
6.00 x 2.60 x 2.35
