shadohead/launchlab-mini/hardware/M5_level_support_v044/references/Added_support_pad_2.stl

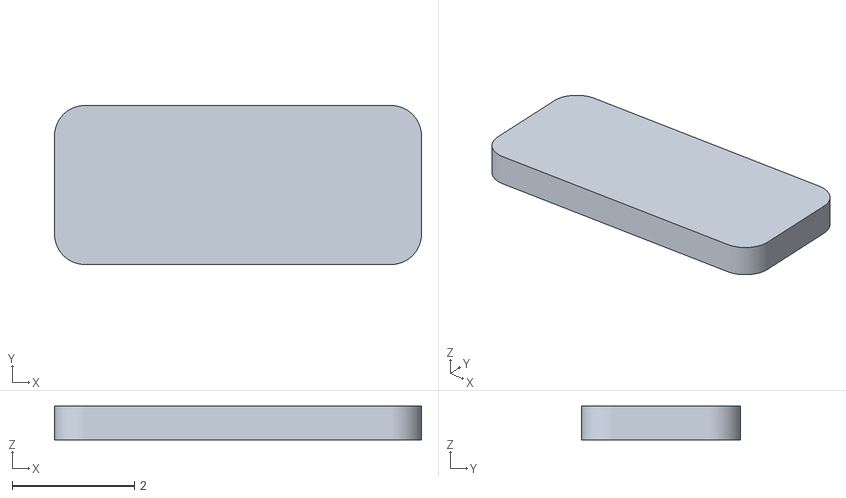
[picture p98: CAD file, 2026-10-03]
hardware/M5_level_support_v044/references/Added_support_pad_2.stl
6.00 x 2.60 x 0.55
