shadohead/launchlab-mini/hardware/M5_raised_rectangle_v046/M5_raised_rectangle_v046_UNSLICED.3mf

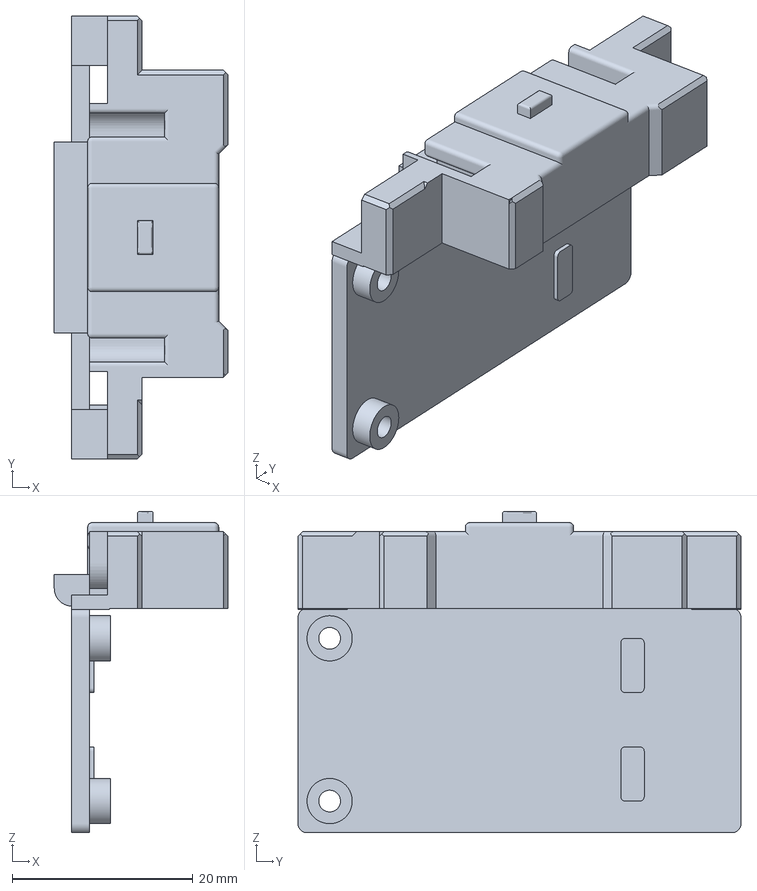
[picture p99: CAD file, 2026-10-03]
hardware/M5_raised_rectangle_v046/M5_raised_rectangle_v046_UNSLICED.3mf
19.2 x 49.0 x 35.6 mm
