shadohead/launchlab-mini/hardware/M5_raised_rectangle_v046/references/Translated_original_rounded_cap.stl

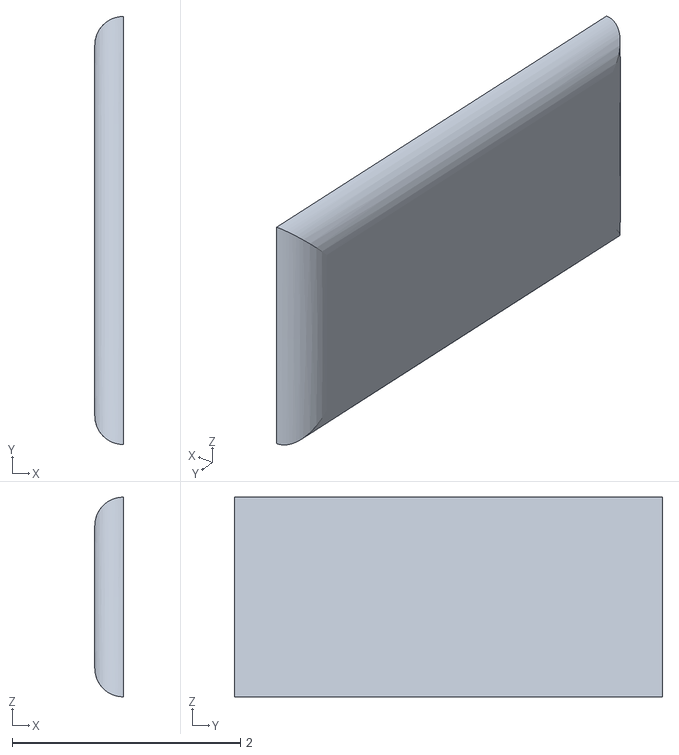
[picture p100: CAD file, 2026-10-03]
hardware/M5_raised_rectangle_v046/references/Translated_original_rounded_cap.stl
0.25 x 3.75 x 1.75
