shadohead/launchlab-mini/hardware/M5_raised_rectangle_v046/step/Added_rectangle_root_ONLY.step

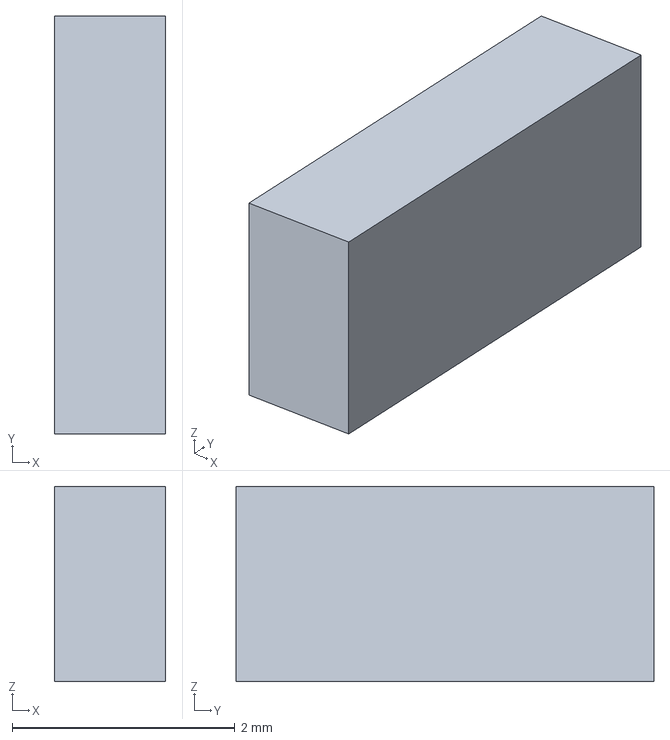
[picture p101: CAD file, 2026-10-03]
hardware/M5_raised_rectangle_v046/step/Added_rectangle_root_ONLY.step
1.00 x 3.75 x 1.75 mm
