shadohead/launchlab-mini/hardware/M5_rotated_rectangle_v047/references/Rotated_actual_rectangle.stl

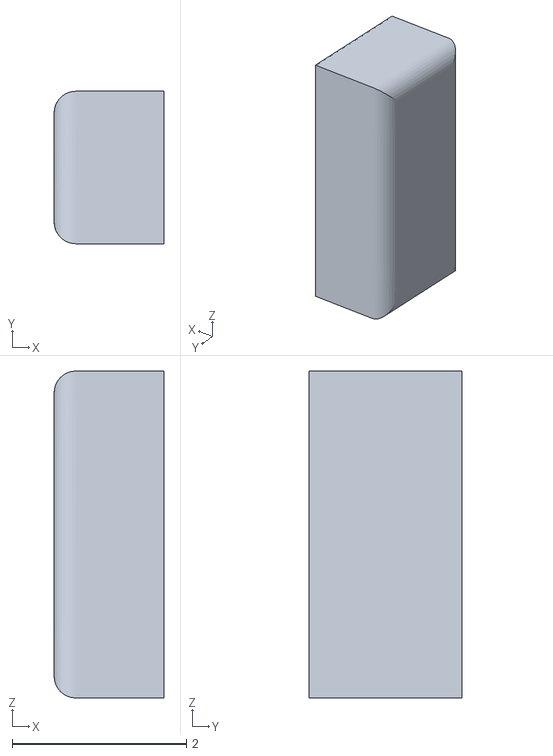
[picture p102: CAD file, 2026-10-03]
hardware/M5_rotated_rectangle_v047/references/Rotated_actual_rectangle.stl
1.26 x 1.75 x 3.75
