shadohead/launchlab-mini/hardware/M5_smooth_rectangle_v048/references/Smoothed_center_tab.stl

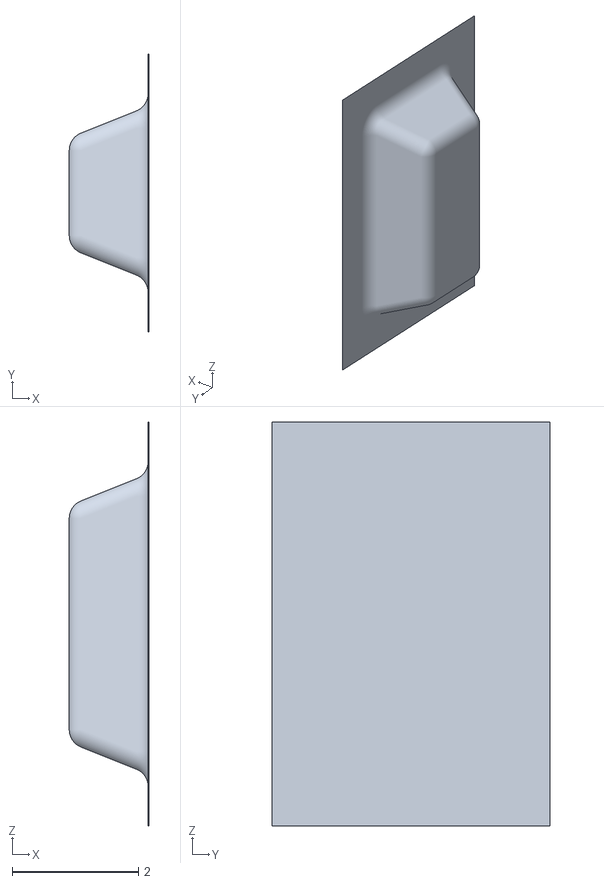
[picture p103: CAD file, 2026-10-03]
hardware/M5_smooth_rectangle_v048/references/Smoothed_center_tab.stl
1.26 x 4.40 x 6.40
