shadohead/launchlab-mini/hardware/M5_soft_ramp_v049/references/Soft_center_ramp.stl

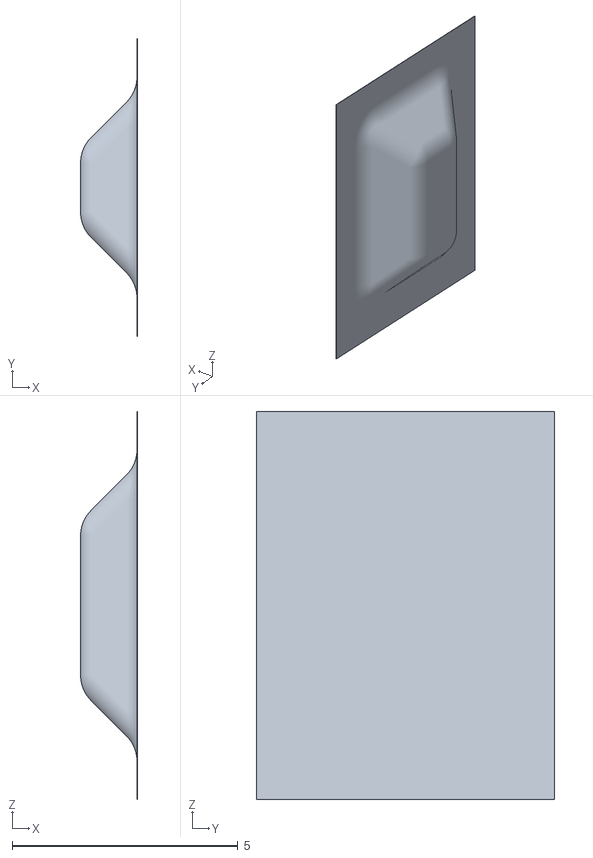
[picture p104: CAD file, 2026-10-03]
hardware/M5_soft_ramp_v049/references/Soft_center_ramp.stl
1.26 x 6.60 x 8.60
