shadohead/launchlab-mini/hardware/minimal_TCRT_sensor_only_v042/step/03_TCRT_sensor_pressure_keeper.step

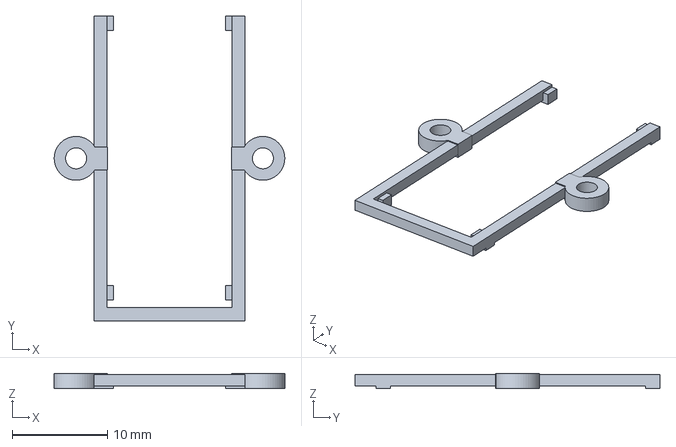
[picture p105: CAD file, 2026-10-03]
hardware/minimal_TCRT_sensor_only_v042/step/03_TCRT_sensor_pressure_keeper.step
24.2 x 32.0 x 1.60 mm
