shadohead/launchlab-mini/hardware/minimal_TCRT_sensor_only_v042/TCRT_sensor_only_v042.step

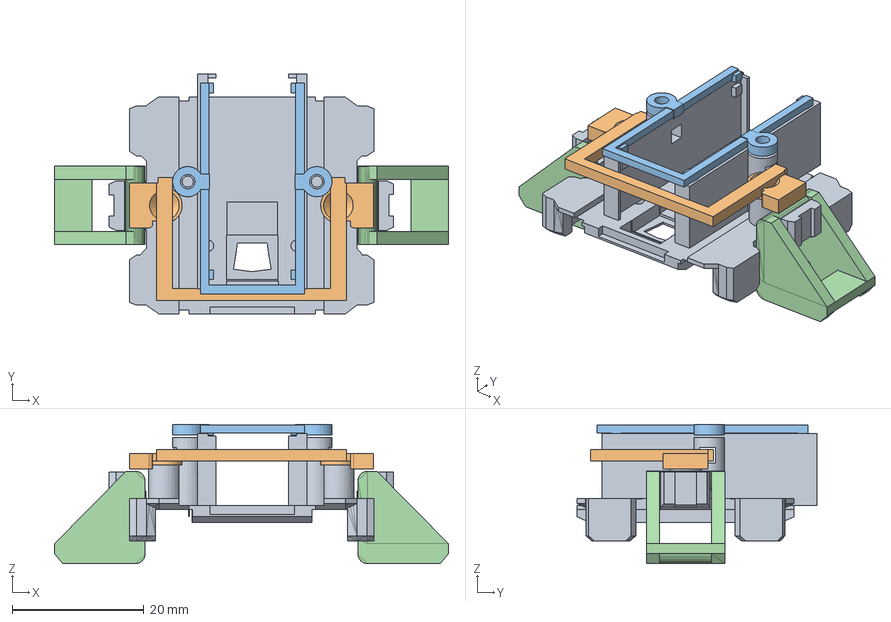
[picture p106: CAD file, 2026-10-03]
hardware/minimal_TCRT_sensor_only_v042/TCRT_sensor_only_v042.step
59.8 x 36.4 x 21.2 mm
