shadohead/launchlab-mini/hardware/minimal_TCRT_split_keepers_v043/step/02_TCRT_clip_cap_LEFT.step

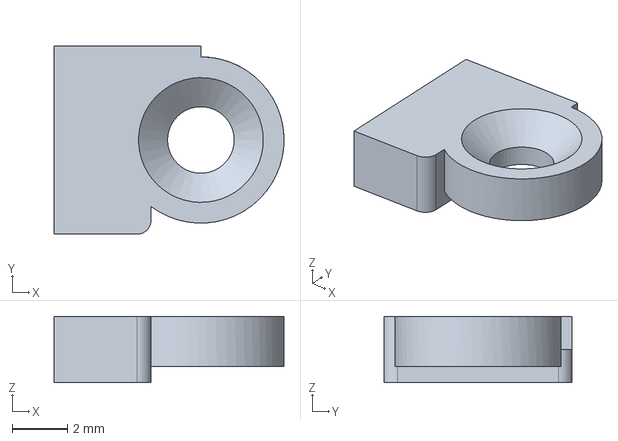
[picture p107: CAD file, 2026-10-03]
hardware/minimal_TCRT_split_keepers_v043/step/02_TCRT_clip_cap_LEFT.step
8.30 x 6.80 x 2.38 mm
