shadohead/launchlab-mini/hardware/minimal_TCRT_split_keepers_v043/TCRT_split_keepers_v043.step

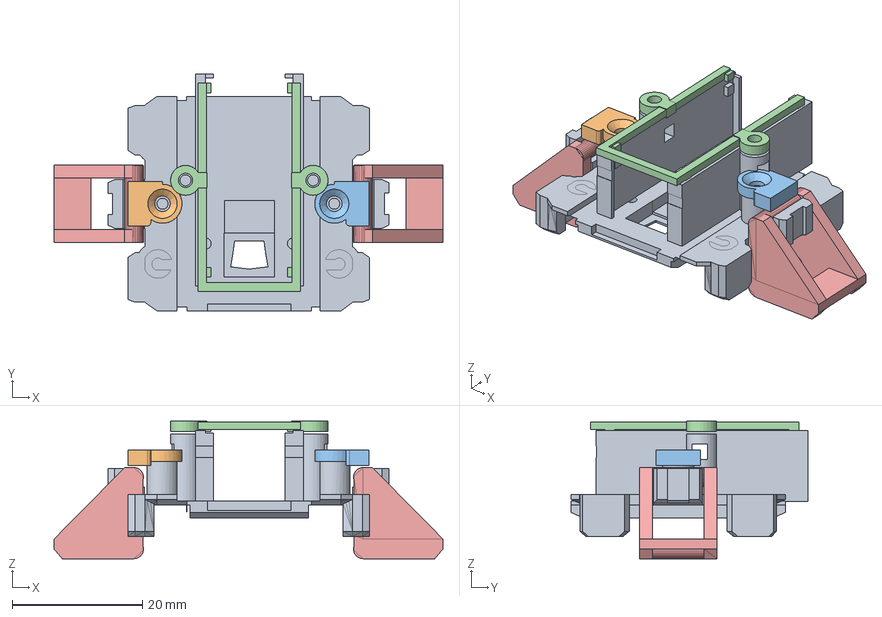
[picture p108: CAD file, 2026-10-03]
hardware/minimal_TCRT_split_keepers_v043/TCRT_split_keepers_v043.step
59.8 x 36.4 x 21.2 mm
