shadohead/launchlab-mini/hardware/minimal_TCRT_stack_v041/preview/REF_TCRT_UNDERSIDE_SOLDER.stl

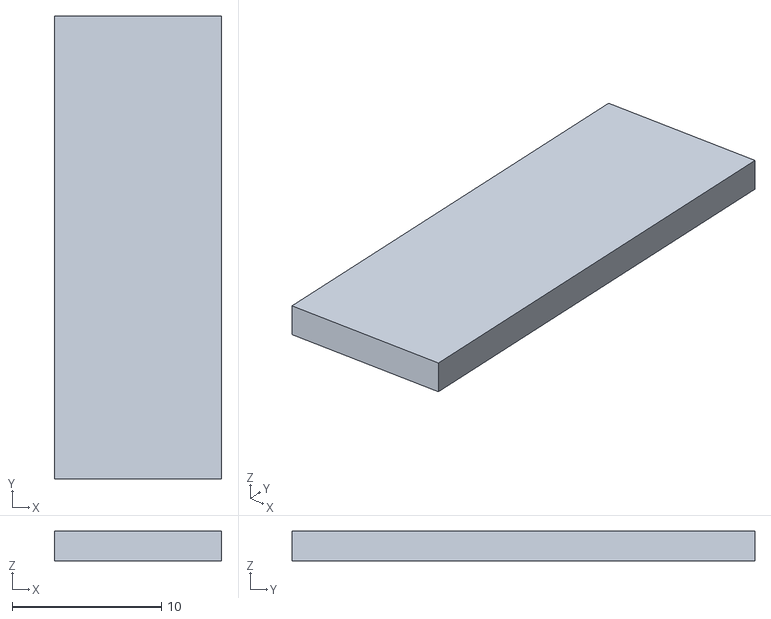
[picture p109: CAD file, 2026-10-03]
hardware/minimal_TCRT_stack_v041/preview/REF_TCRT_UNDERSIDE_SOLDER.stl
11.2 x 31.0 x 2.00
