shadohead/launchlab-mini/hardware/minimal_TCRT_stack_v041/step/02_TCRT_clip_keeper.step

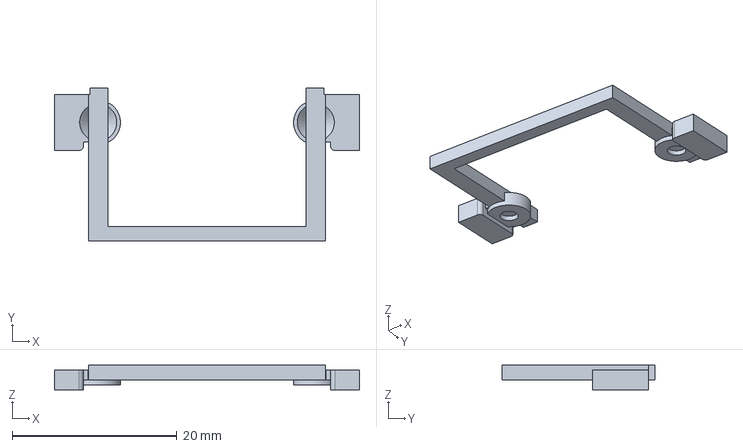
[picture p110: CAD file, 2026-10-03]
hardware/minimal_TCRT_stack_v041/step/02_TCRT_clip_keeper.step
37.0 x 18.6 x 2.98 mm
