shadohead/launchlab-mini/hardware/minimal_TCRT_stack_v041/stl/09_TCRT_latch_RIGHT.stl

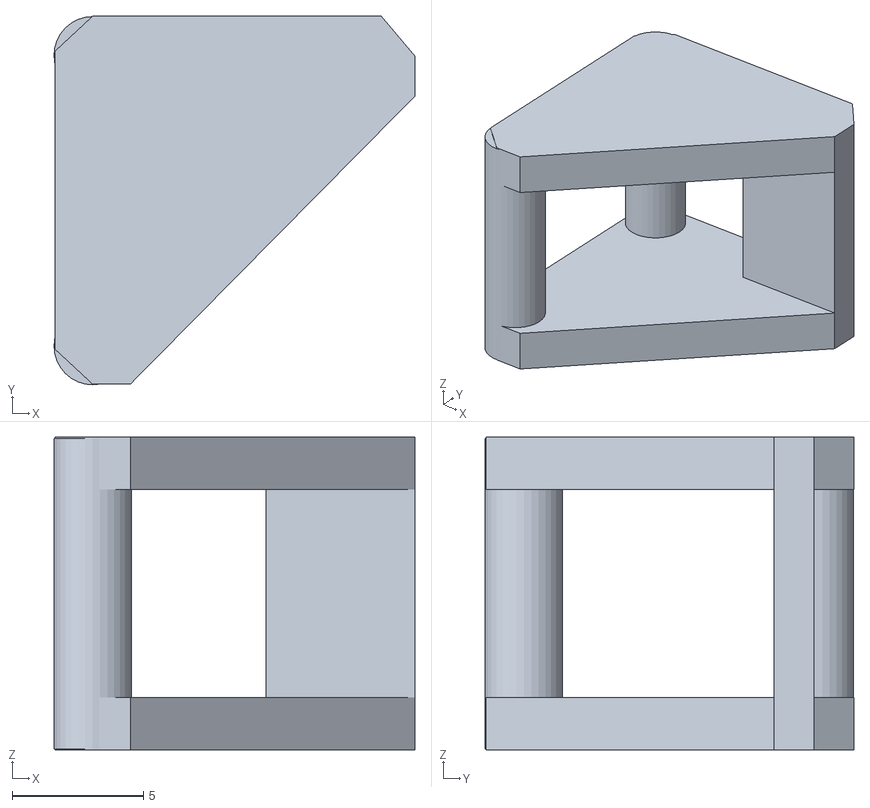
[picture p111: CAD file, 2026-10-02]
hardware/minimal_TCRT_stack_v041/stl/09_TCRT_latch_RIGHT.stl
13.7 x 14.0 x 11.9
