shadohead/launchlab-mini/hardware/minimal_TCRT_stack_v041/TCRT_minimal_stack_v041.step

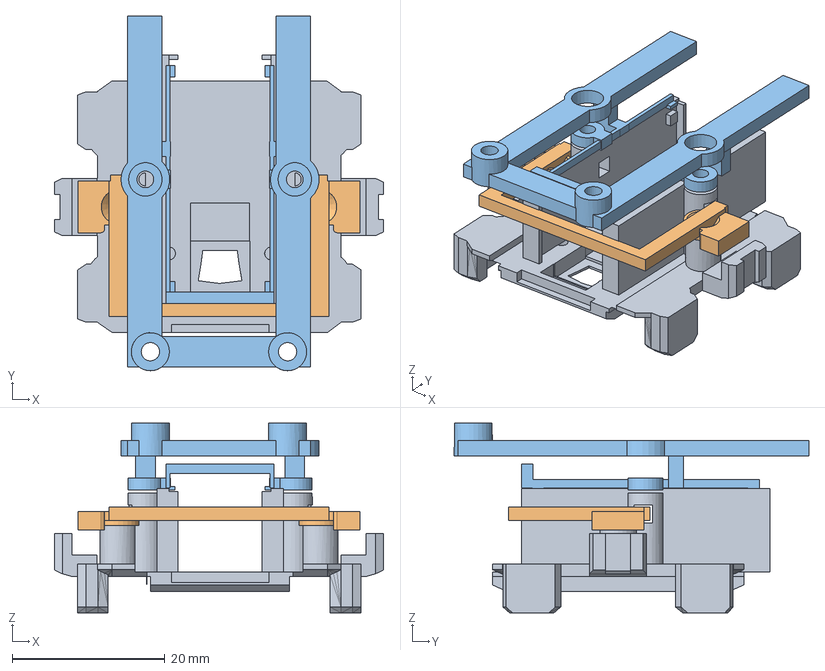
[picture p112: CAD file, 2026-10-03]
hardware/minimal_TCRT_stack_v041/TCRT_minimal_stack_v041.step
43.1 x 46.5 x 24.9 mm
