shadohead/launchlab-mini/hardware/LaunchLab_v019_tcrt5000_open_stack/bambu/LaunchLab_v019_P1S_PLA_PORT.3mf

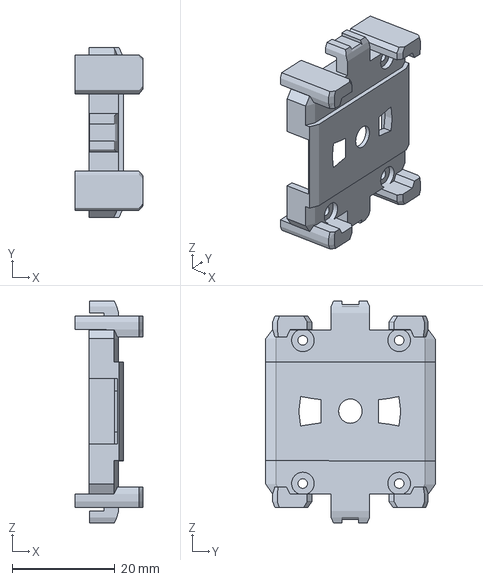
[picture p113: CAD file, 2026-10-03]
hardware/LaunchLab_v019_tcrt5000_open_stack/bambu/LaunchLab_v019_P1S_PLA_PORT.3mf
13.3 x 33.0 x 43.1 mm
