shadohead/launchlab-mini/hardware/LaunchLab_v019_tcrt5000_open_stack/LaunchLab_v019_SENSOR_FIT_UNSLICED.3mf

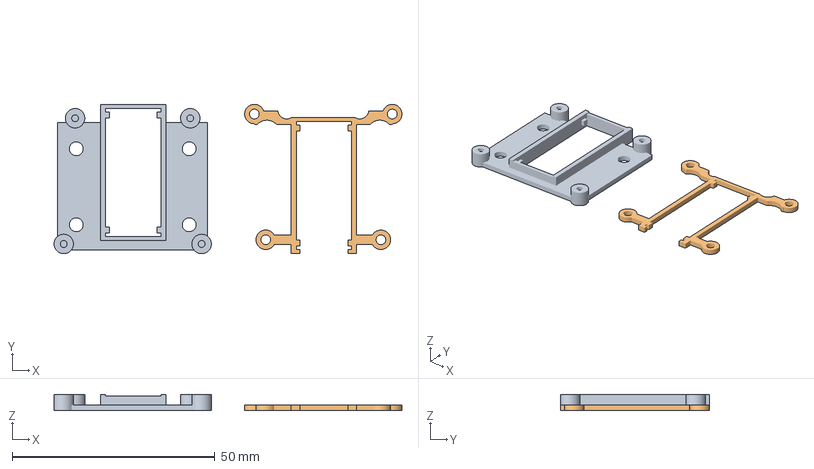
[picture p114: CAD file, 2026-10-03]
hardware/LaunchLab_v019_tcrt5000_open_stack/LaunchLab_v019_SENSOR_FIT_UNSLICED.3mf
85.8 x 36.8 x 4.02 mm
11_TCRT_SEAT_FIT
12_TCRT_KEEPER_FIT
