shadohead/launchlab-mini/hardware/LaunchLab_v019_tcrt5000_open_stack/preview/REF_TCRT_TOP_SOLDER.stl

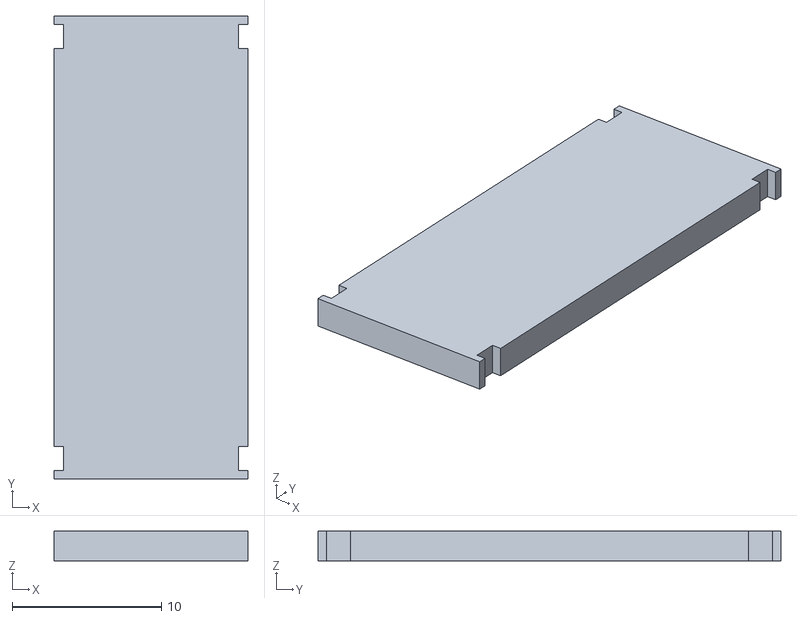
[picture p115: CAD file, 2026-10-03]
hardware/LaunchLab_v019_tcrt5000_open_stack/preview/REF_TCRT_TOP_SOLDER.stl
13.0 x 31.0 x 2.00
