shadohead/launchlab-mini/hardware/LaunchLab_v033_flush_QRE/preview/REF_QRE_downward_optics.stl

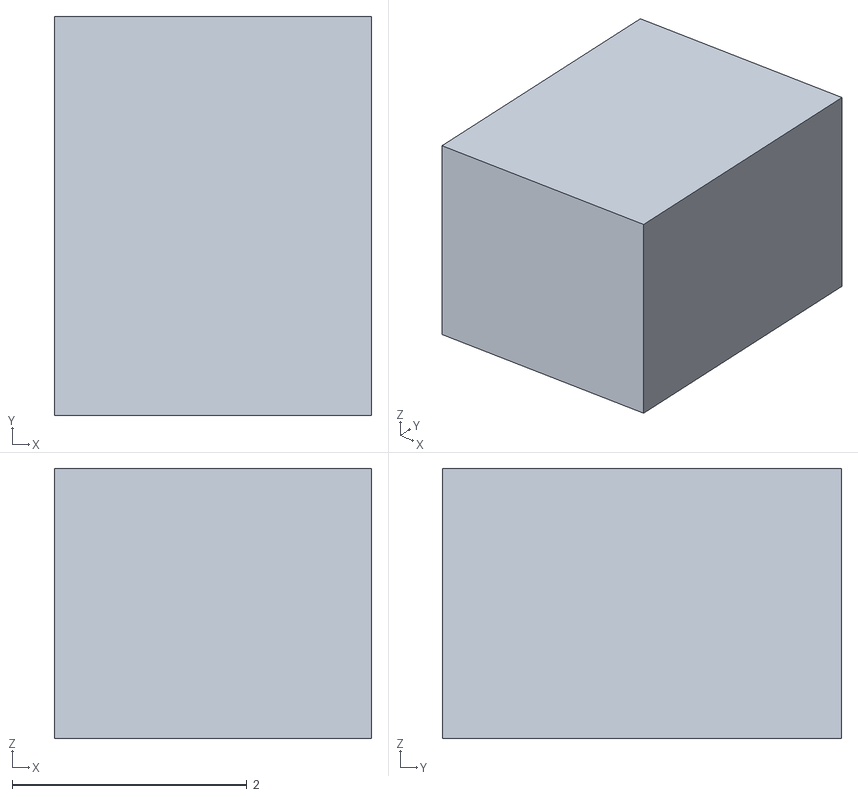
[picture p116: CAD file, 2026-10-02]
hardware/LaunchLab_v033_flush_QRE/preview/REF_QRE_downward_optics.stl
2.70 x 3.40 x 2.30
