shadohead/launchlab-mini/hardware/LaunchLab_v033_flush_QRE/references/REF_section_base.stl

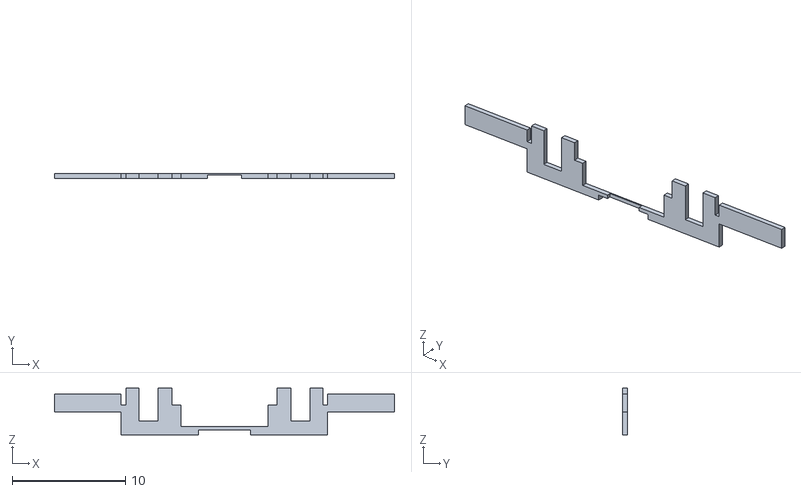
[picture p117: CAD file, 2026-10-02]
hardware/LaunchLab_v033_flush_QRE/references/REF_section_base.stl
30.0 x 0.4 x 4.12
