shadohead/launchlab-mini/hardware/LaunchLab_v040_right_block_print/preview/REF_soft_liner_1.stl

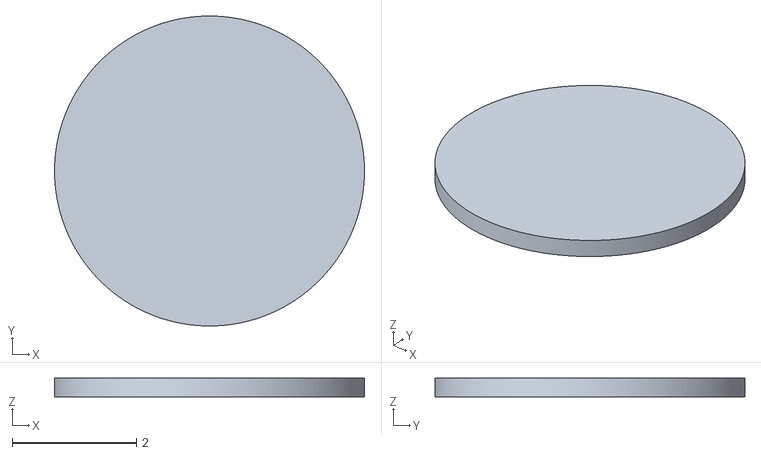
[picture p118: CAD file, 2026-10-02]
hardware/LaunchLab_v040_right_block_print/preview/REF_soft_liner_1.stl
5.00 x 5.00 x 0.3
