shadohead/launchlab-mini/hardware/M5_cable_hook_v068/preview/REF_M2x6_2.stl

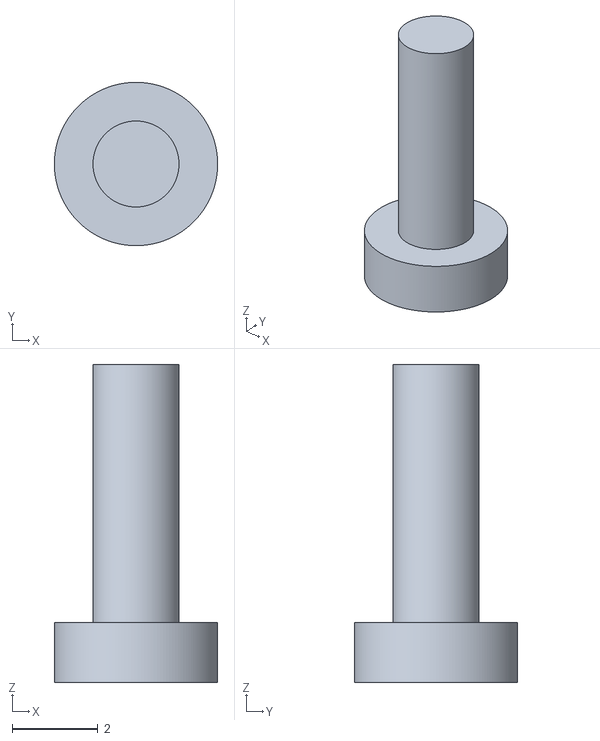
[picture p119: CAD file, 2026-10-02]
hardware/M5_cable_hook_v068/preview/REF_M2x6_2.stl
3.80 x 3.80 x 7.40
