shadohead/launchlab-mini/hardware/minimal_TCRT_sensor_only_v042/step/01_TCRT_sensor_cradle.step

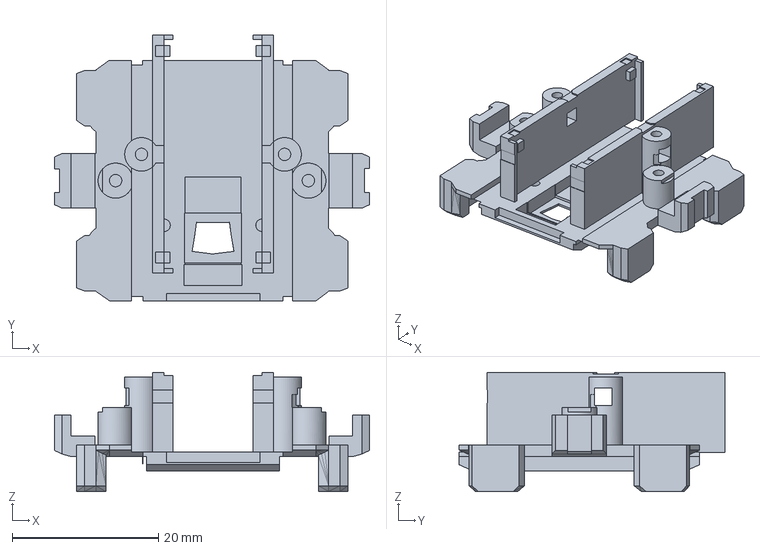
[picture p120: CAD file, 2026-10-03]
hardware/minimal_TCRT_sensor_only_v042/step/01_TCRT_sensor_cradle.step
43.1 x 36.4 x 16.3 mm
