shadohead/launchlab-mini/hardware/minimal_TCRT_split_keepers_v043/preview/REF_TCRT_HEAD_AND_LEGS.stl

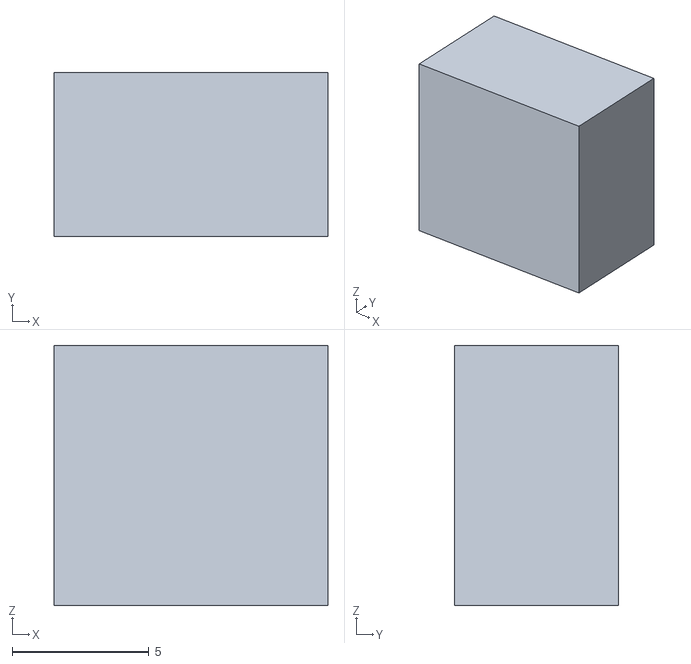
[picture p121: CAD file, 2026-10-03]
hardware/minimal_TCRT_split_keepers_v043/preview/REF_TCRT_HEAD_AND_LEGS.stl
10.0 x 6.00 x 9.50
