shadohead/launchlab-mini/hardware/LaunchLab_v019_tcrt5000_open_stack/extras/11_TCRT_SEAT_FIT.step

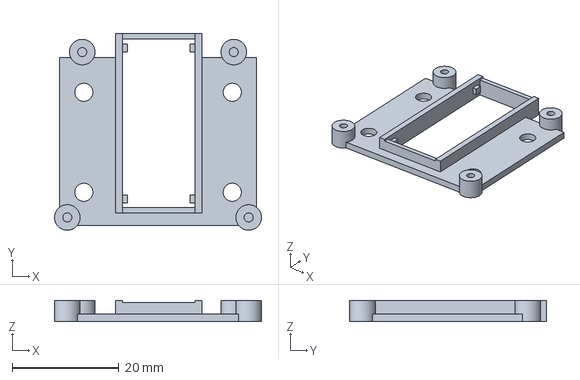
[picture p122: CAD file, 2026-10-03]
hardware/LaunchLab_v019_tcrt5000_open_stack/extras/11_TCRT_SEAT_FIT.step
38.8 x 36.8 x 4.02 mm
