shadohead/launchlab-mini/hardware/LaunchLab_v019_tcrt5000_open_stack/step/04_TCRT_M5_top_dock.step

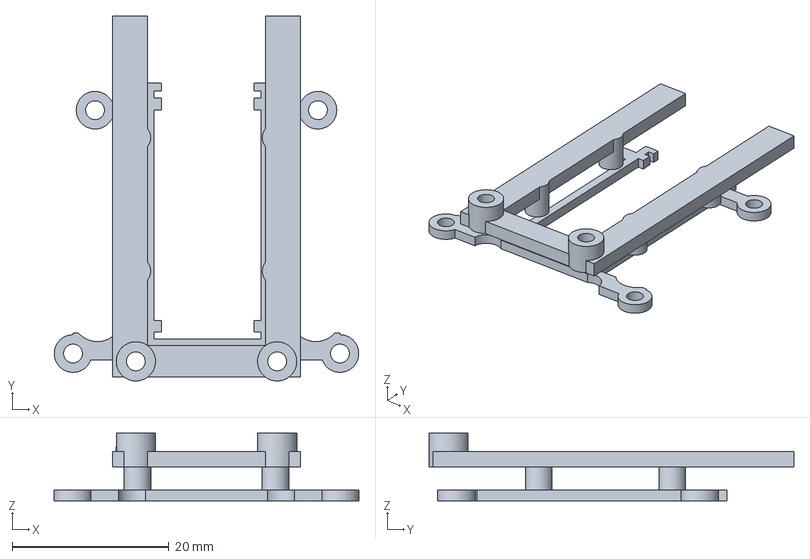
[picture p124: CAD file, 2026-10-03]
hardware/LaunchLab_v019_tcrt5000_open_stack/step/04_TCRT_M5_top_dock.step
38.8 x 46.5 x 8.60 mm
