shadohead/launchlab-mini/hardware/LaunchLab_v033_flush_QRE/references/REF_side_relief.step

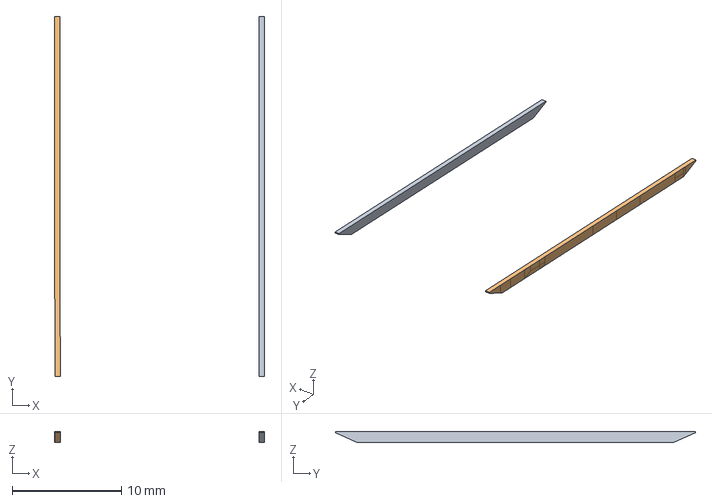
[picture p125: CAD file, 2026-10-02]
hardware/LaunchLab_v033_flush_QRE/references/REF_side_relief.step
19.2 x 32.9 x 1.00 mm
