shadohead/launchlab-mini/hardware/M5_cable_hook_v068/preview/REF_M5Stick_factory_geometry.stl

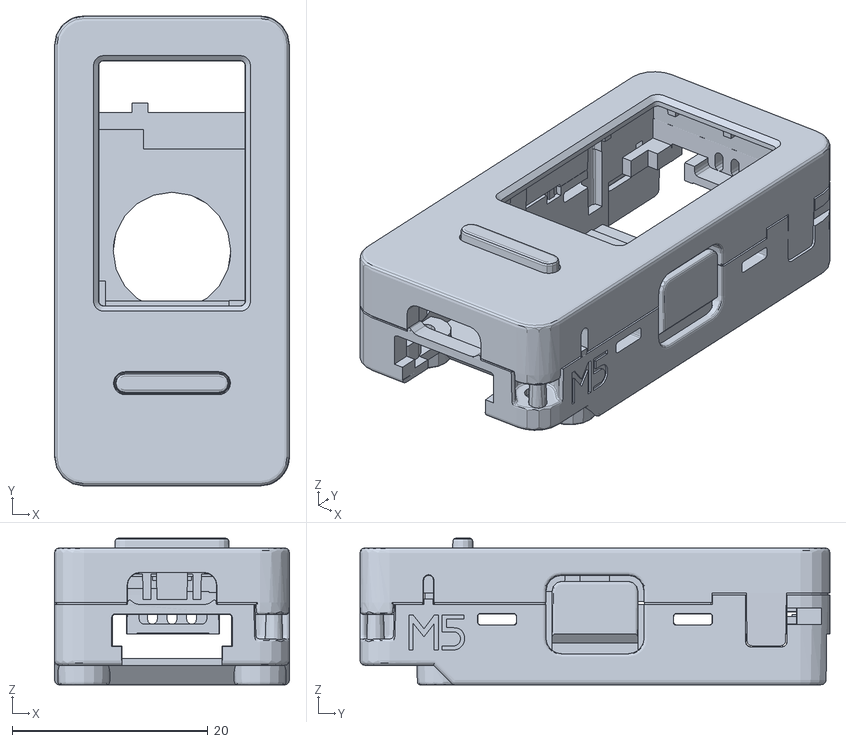
[picture p126: CAD file, 2026-10-02]
hardware/M5_cable_hook_v068/preview/REF_M5Stick_factory_geometry.stl
24.0 x 48.0 x 15.0
