shadohead/launchlab-mini/hardware/M5_cable_hook_v068/references/REF_hook_wire_3.stl

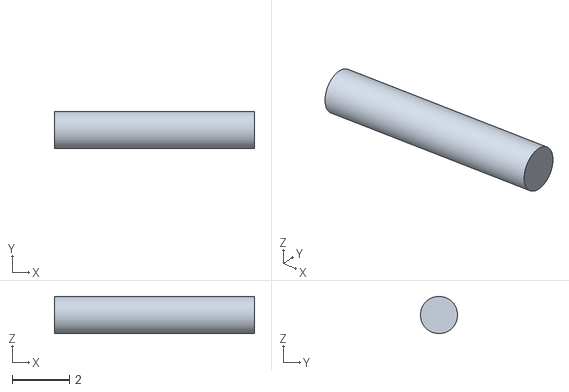
[picture p127: CAD file, 2026-10-05]
hardware/M5_cable_hook_v068/references/REF_hook_wire_3.stl
7.00 x 1.30 x 1.30
