shadohead/launchlab-mini/hardware/minimal_TCRT_stack_v041/preview/REF_TCRT_HEADER.stl

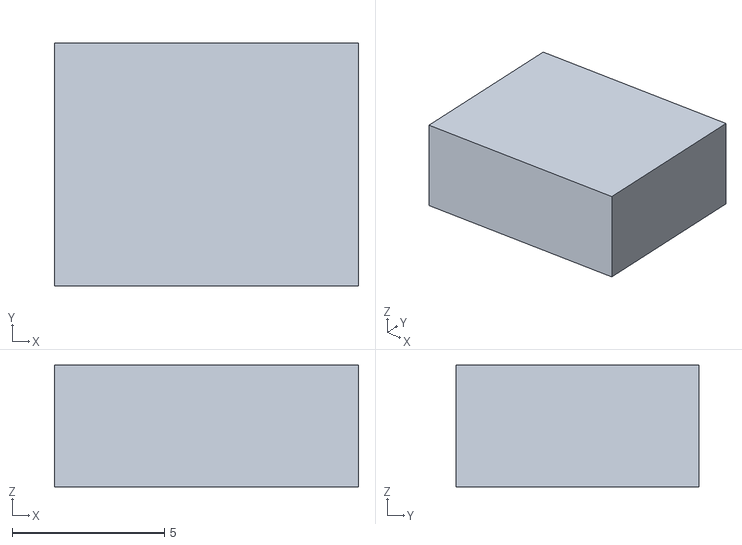
[picture p128: CAD file, 2026-10-03]
hardware/minimal_TCRT_stack_v041/preview/REF_TCRT_HEADER.stl
10.0 x 8.00 x 4.00
