shadohead/launchlab-mini/hardware/minimal_TCRT_stack_v041/step/03_TCRT_M5_clamp_dock.step

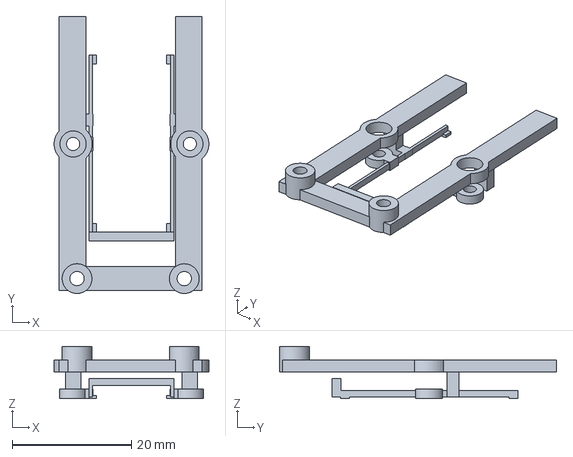
[picture p129: CAD file, 2026-10-03]
hardware/minimal_TCRT_stack_v041/step/03_TCRT_M5_clamp_dock.step
26.0 x 46.5 x 8.80 mm
