shadohead/launchlab-mini/hardware/LaunchLab_v019_tcrt5000_open_stack/bambu/LaunchLab_v019_P1S_PLA_REPLACEMENTS.3mf

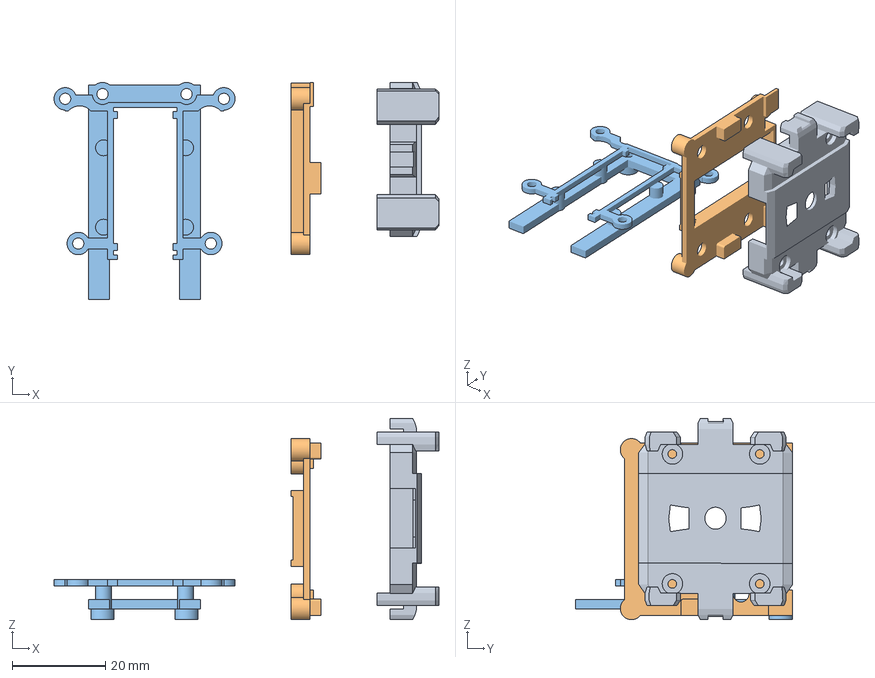
[picture p130: CAD file, 2026-10-03]
hardware/LaunchLab_v019_tcrt5000_open_stack/bambu/LaunchLab_v019_P1S_PLA_REPLACEMENTS.3mf
82.5 x 46.5 x 43.1 mm
01_TCRT_attachment_port.001
03_TCRT_sensor_cradle.001
04_TCRT_M5_top_dock.001
