shadohead/launchlab-mini/hardware/LaunchLab_v019_tcrt5000_open_stack/LaunchLab_v019_CLIPS_UNSLICED.3mf

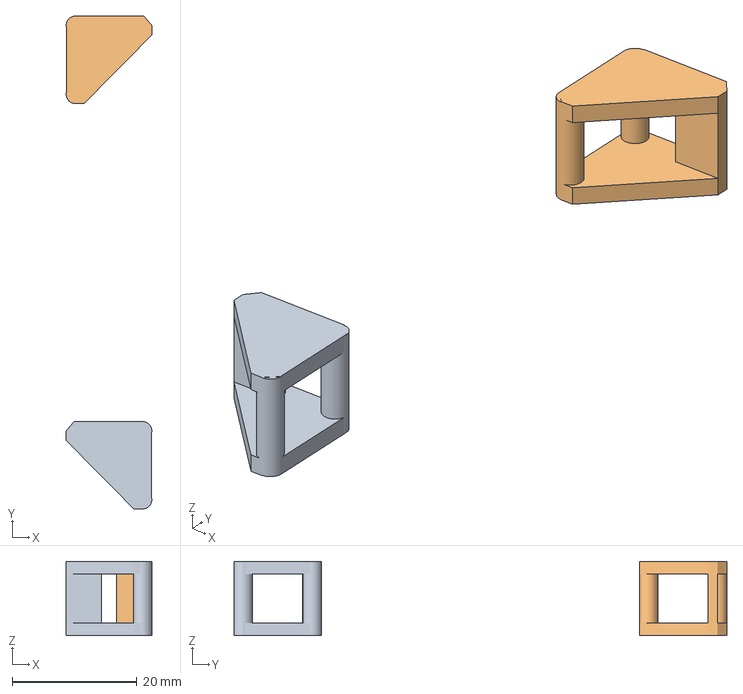
[picture p131: CAD file, 2026-10-03]
hardware/LaunchLab_v019_tcrt5000_open_stack/LaunchLab_v019_CLIPS_UNSLICED.3mf
13.7 x 79.0 x 11.9 mm
02_latch_LEFT.001
02_latch_RIGHT.001
