shadohead/launchlab-mini/hardware/LaunchLab_v019_tcrt5000_open_stack/preview/REF_M3x8_MOUNT_2.stl

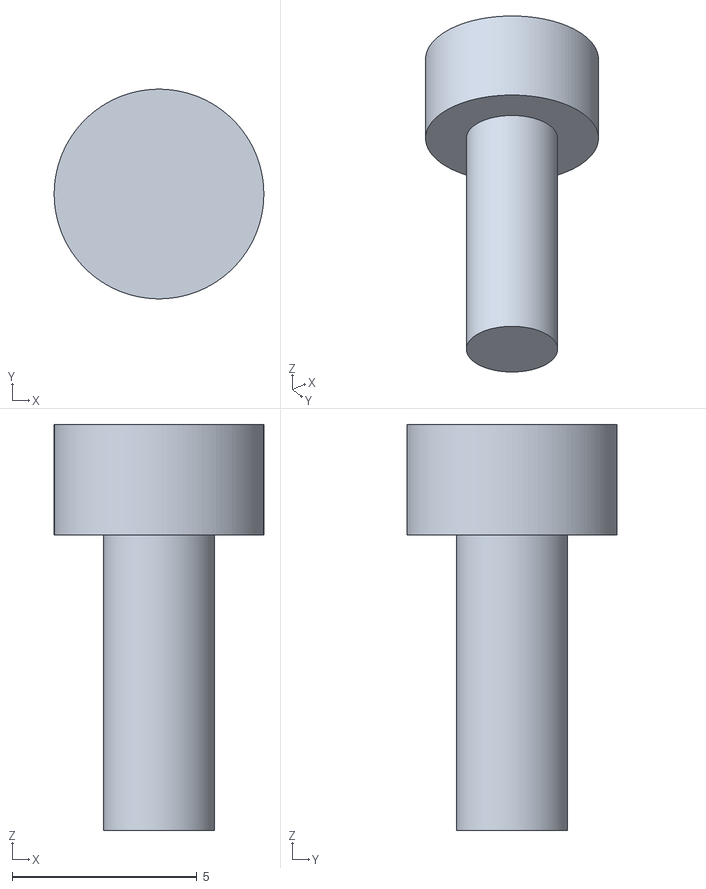
[picture p132: CAD file, 2026-10-03]
hardware/LaunchLab_v019_tcrt5000_open_stack/preview/REF_M3x8_MOUNT_2.stl
5.68 x 5.68 x 11.0
