shadohead/launchlab-mini/hardware/LaunchLab_v033_flush_QRE/preview/REF_QRE_red_PCB.stl

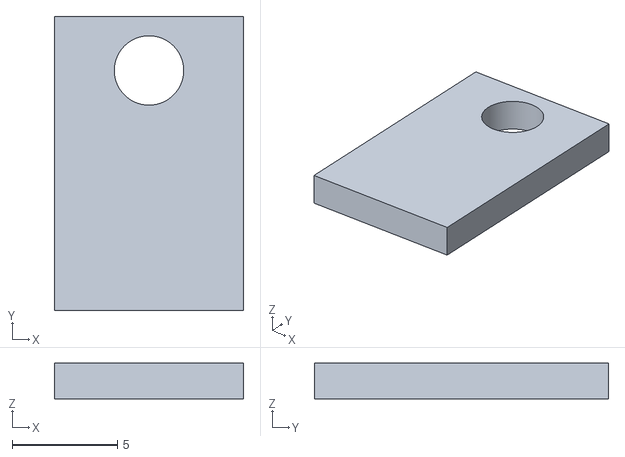
[picture p133: CAD file, 2026-10-02]
hardware/LaunchLab_v033_flush_QRE/preview/REF_QRE_red_PCB.stl
9.00 x 14.0 x 1.70
