shadohead/launchlab-mini/hardware/M5_raised_rectangle_v046/references/SECTION_original_rectangle.stl

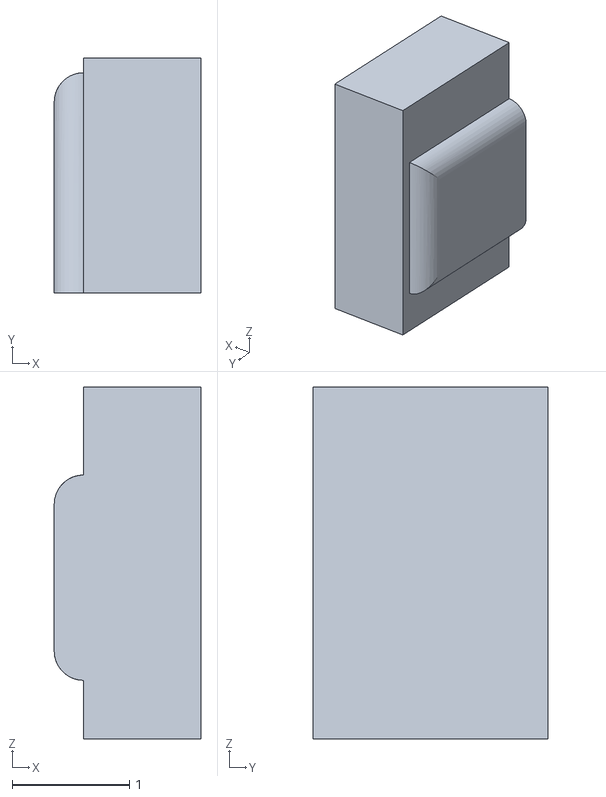
[picture p134: CAD file, 2026-10-03]
hardware/M5_raised_rectangle_v046/references/SECTION_original_rectangle.stl
1.25 x 2.00 x 3.00
