shadohead/launchlab-mini/hardware/LaunchLab_v019_tcrt5000_open_stack/bambu/LaunchLab_v019_P1S_PLA_CLIPS.3mf

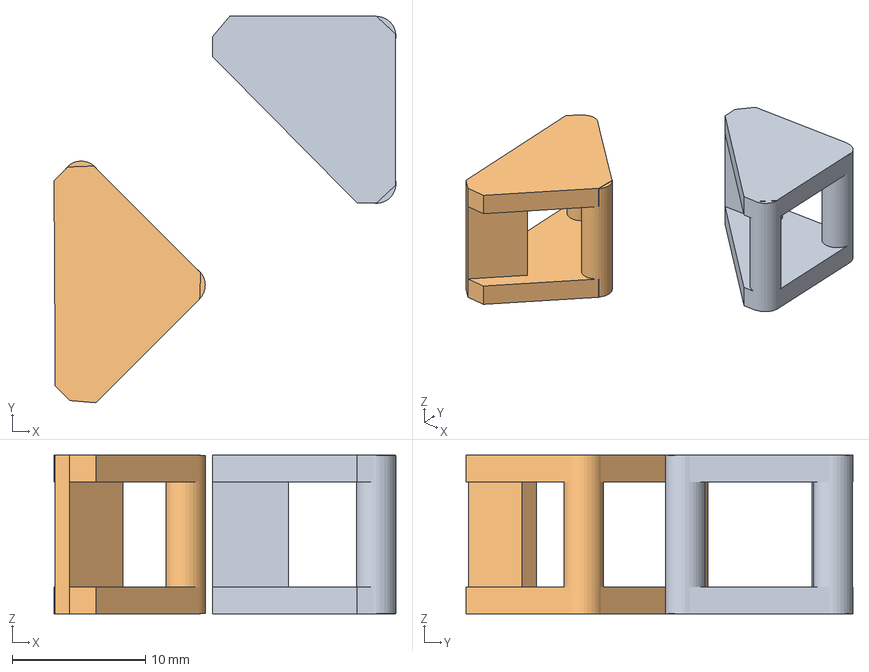
[picture p135: CAD file, 2026-10-03]
hardware/LaunchLab_v019_tcrt5000_open_stack/bambu/LaunchLab_v019_P1S_PLA_CLIPS.3mf
25.6 x 29.0 x 11.9 mm
02_latch_LEFT.001
02_latch_RIGHT.001
