shadohead/launchlab-mini/hardware/LaunchLab_v033_flush_QRE/preview/REF_M2x5_CLIP_1.stl

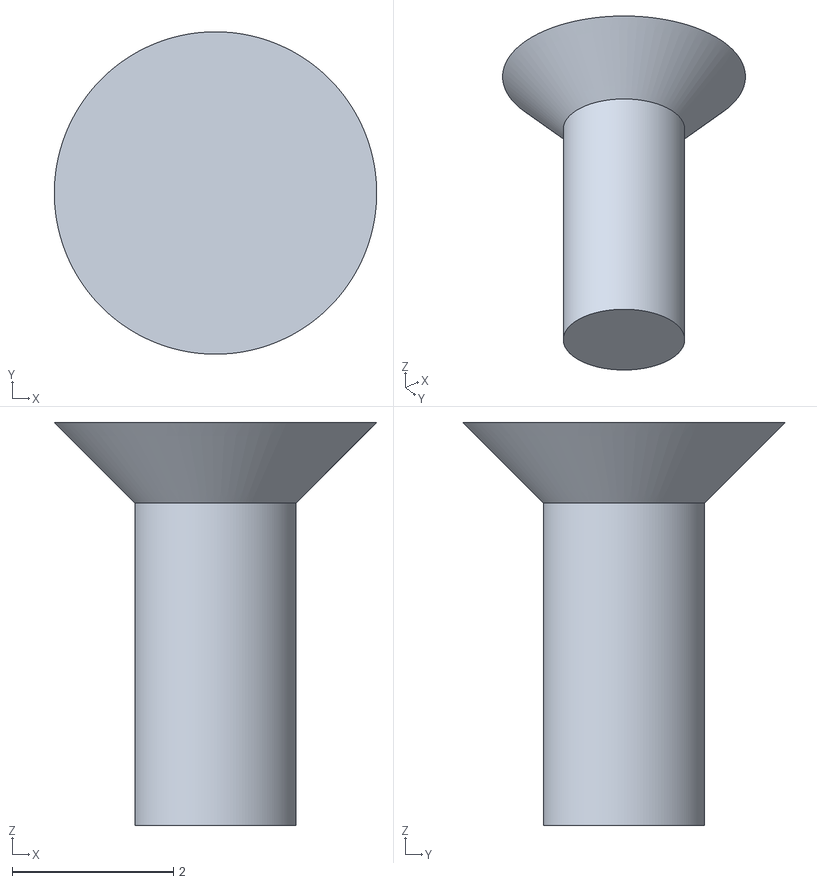
[picture p136: CAD file, 2026-10-02]
hardware/LaunchLab_v033_flush_QRE/preview/REF_M2x5_CLIP_1.stl
4.00 x 4.00 x 5.00
