shadohead/launchlab-mini/hardware/LaunchLab_v033_flush_QRE/references/REF_section_PCB.stl

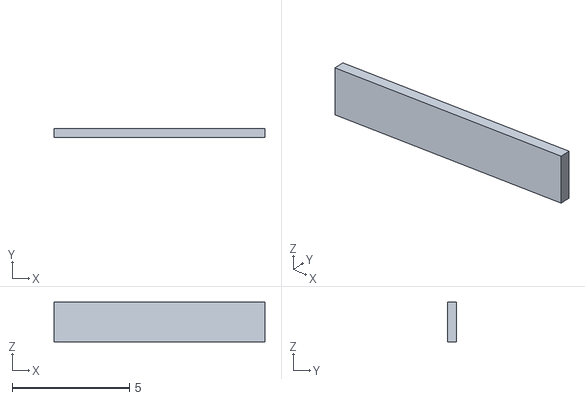
[picture p137: CAD file, 2026-10-02]
hardware/LaunchLab_v033_flush_QRE/references/REF_section_PCB.stl
9.00 x 0.4 x 1.70
