shadohead/launchlab-mini/hardware/M5_cable_hook_v068/preview/REF_Display_visual.stl

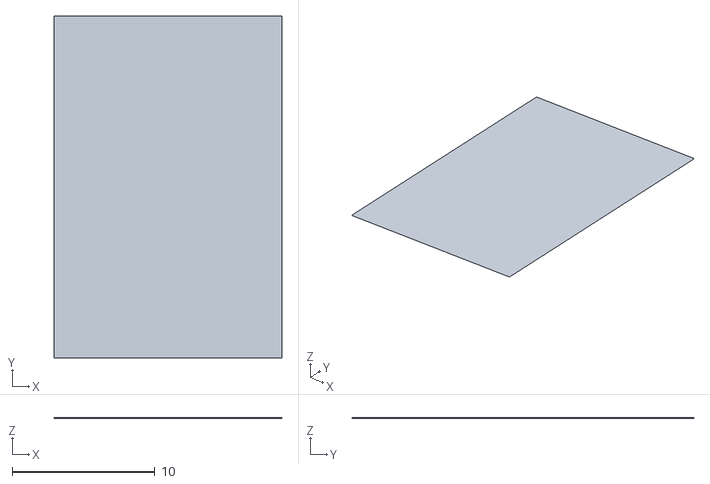
[picture p138: CAD file, 2026-10-02]
hardware/M5_cable_hook_v068/preview/REF_Display_visual.stl
16.0 x 24.0 x 0.04
