shadohead/launchlab-mini/hardware/M5_raised_rectangle_v046/references/SECTION_revised_rectangle.stl

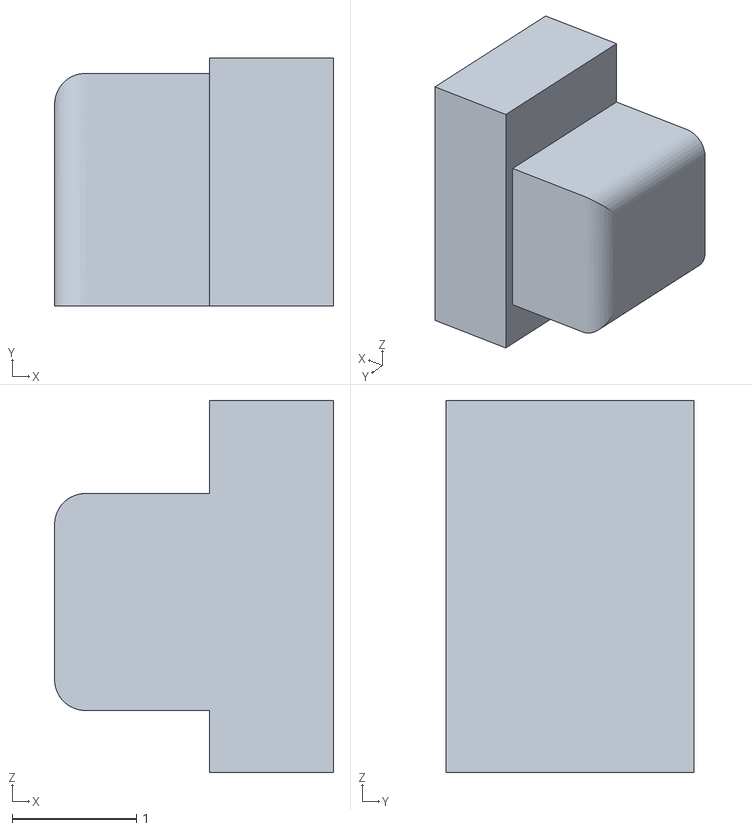
[picture p139: CAD file, 2026-10-03]
hardware/M5_raised_rectangle_v046/references/SECTION_revised_rectangle.stl
2.25 x 2.00 x 3.00
