shadohead/launchlab-mini/hardware/LaunchLab_v019_tcrt5000_open_stack/bambu/LaunchLab_v019_P1S_PLA_ALL_PARTS.3mf

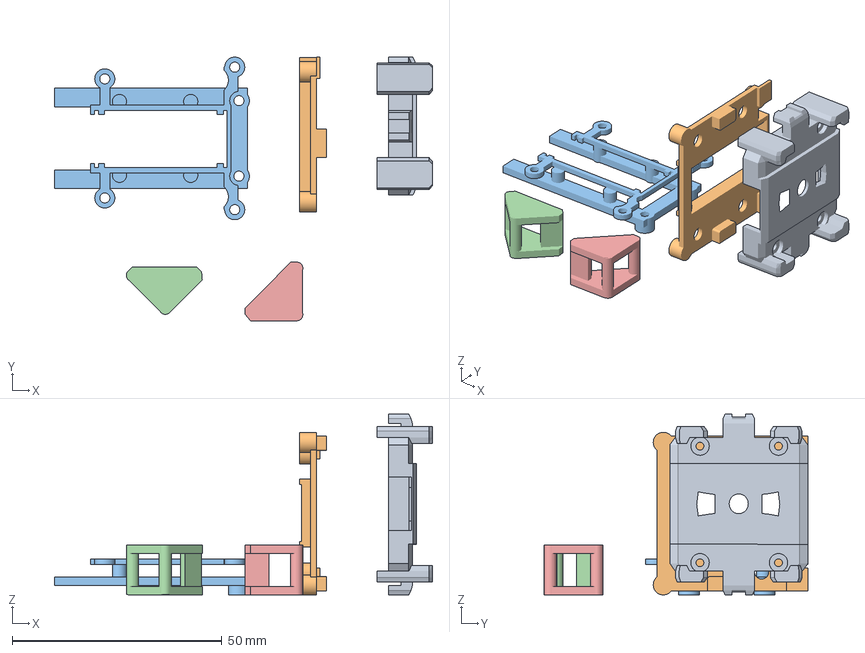
[picture p140: CAD file, 2026-10-03]
hardware/LaunchLab_v019_tcrt5000_open_stack/bambu/LaunchLab_v019_P1S_PLA_ALL_PARTS.3mf
90.2 x 62.9 x 43.1 mm
01_TCRT_attachment_port.001
03_TCRT_sensor_cradle.001
04_TCRT_M5_top_dock.001
02_latch_LEFT.001
02_latch_RIGHT.001
