shadohead/launchlab-mini/hardware/LaunchLab_v033_flush_QRE/preview/REF_QRE_existing_upright_plug_2.stl

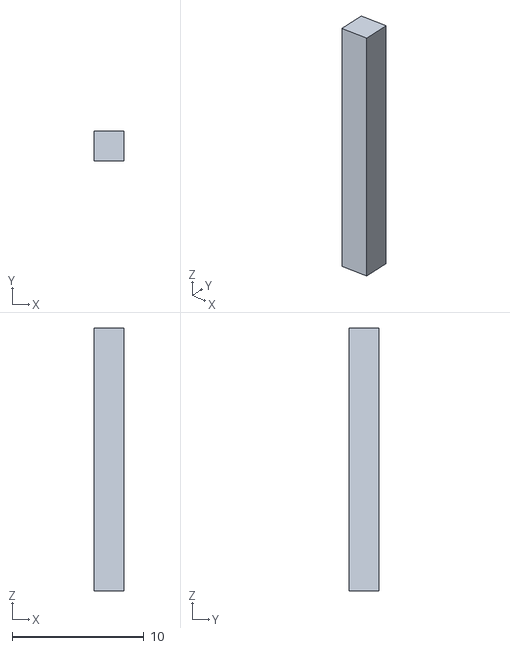
[picture p141: CAD file, 2026-10-02]
hardware/LaunchLab_v033_flush_QRE/preview/REF_QRE_existing_upright_plug_2.stl
2.30 x 2.30 x 20.0
