shadohead/launchlab-mini/hardware/LaunchLab_v033_flush_QRE/references/REF_section_bar.stl

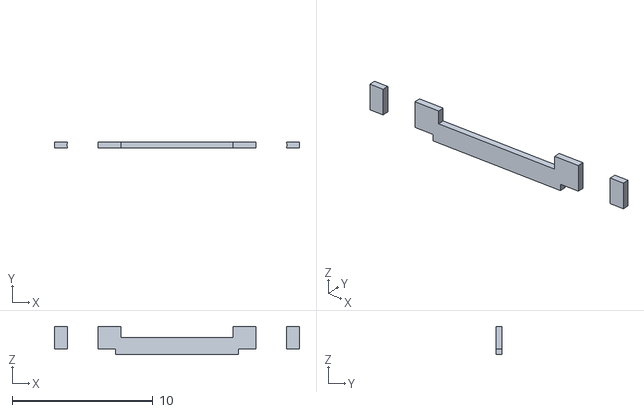
[picture p142: CAD file, 2026-10-02]
hardware/LaunchLab_v033_flush_QRE/references/REF_section_bar.stl
17.4 x 0.4 x 2.00
