shadohead/launchlab-mini/hardware/M5_cable_hook_v068/references/REF_channel_cutter.stl

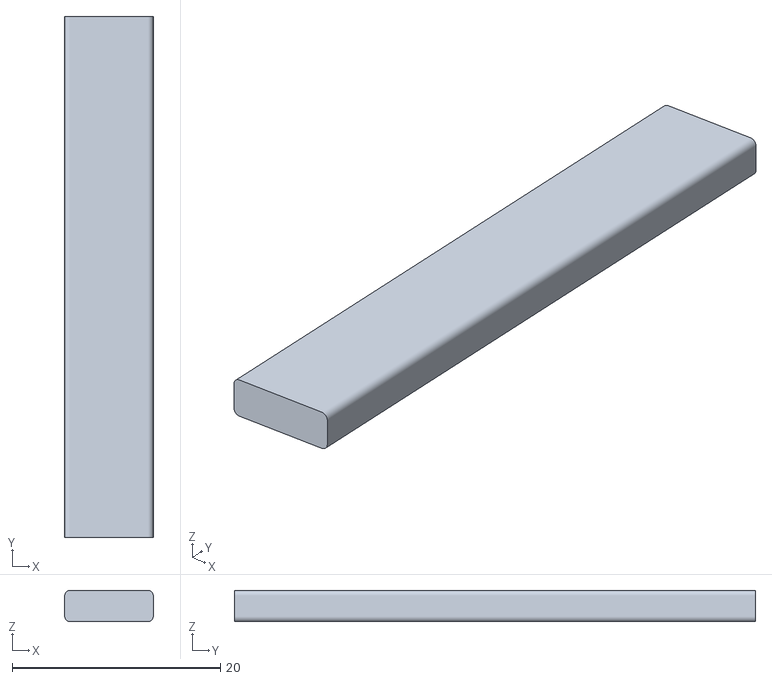
[picture p143: CAD file, 2026-10-05]
hardware/M5_cable_hook_v068/references/REF_channel_cutter.stl
8.50 x 50.0 x 3.00
