shadohead/launchlab-mini/hardware/LaunchLab_v033_flush_QRE/preview/REF_Underside_resistor_-1.524.stl

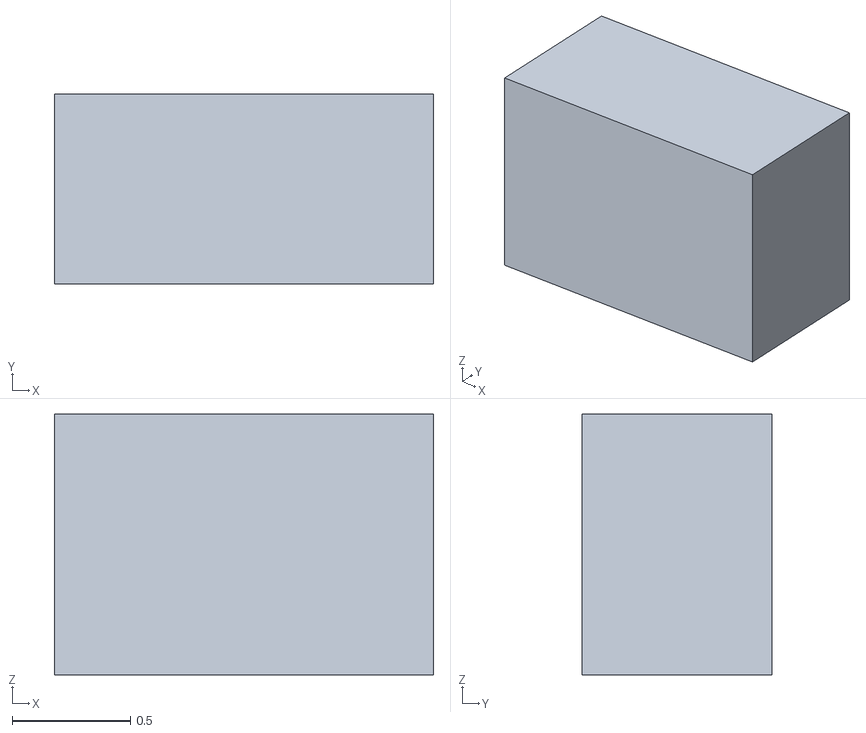
[picture p144: CAD file, 2026-10-02]
hardware/LaunchLab_v033_flush_QRE/preview/REF_Underside_resistor_-1.524.stl
1.60 x 0.8 x 1.10
