shadohead/launchlab-mini/hardware/LaunchLab_v019_tcrt5000_open_stack/renders/01_assembled.png

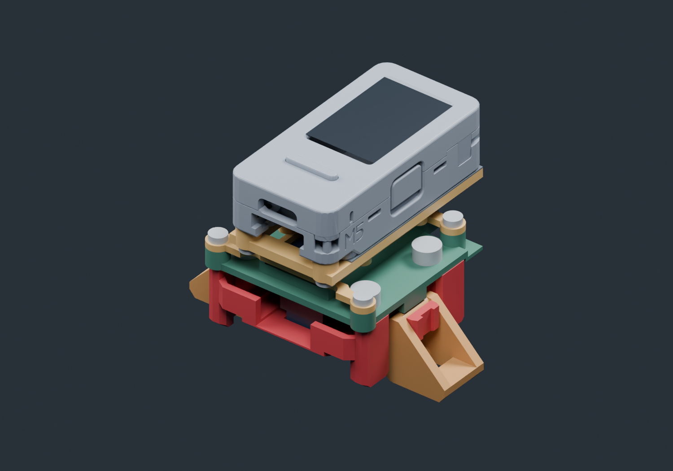
hardware/LaunchLab_v019_tcrt5000_open_stack/renders/01_assembled.png
