shadohead/launchlab-mini/hardware/LaunchLab_v040_right_block_print/references/USER_circled_topdown.png

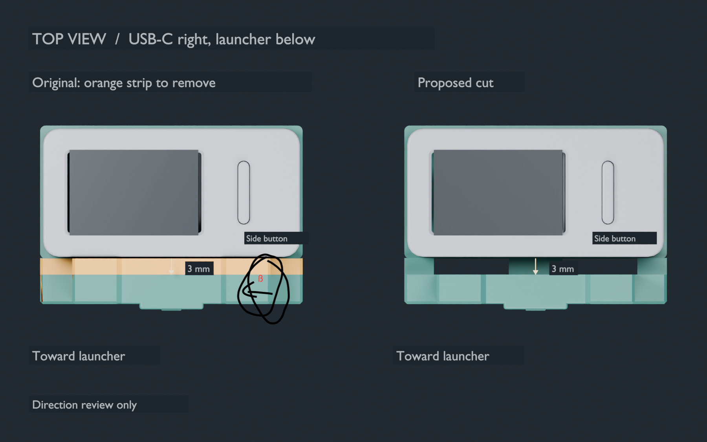
hardware/LaunchLab_v040_right_block_print/references/USER_circled_topdown.png
