shadohead/launchlab-mini/hardware/LaunchLab_v040_right_block_print/renders/03_bare_mount.png

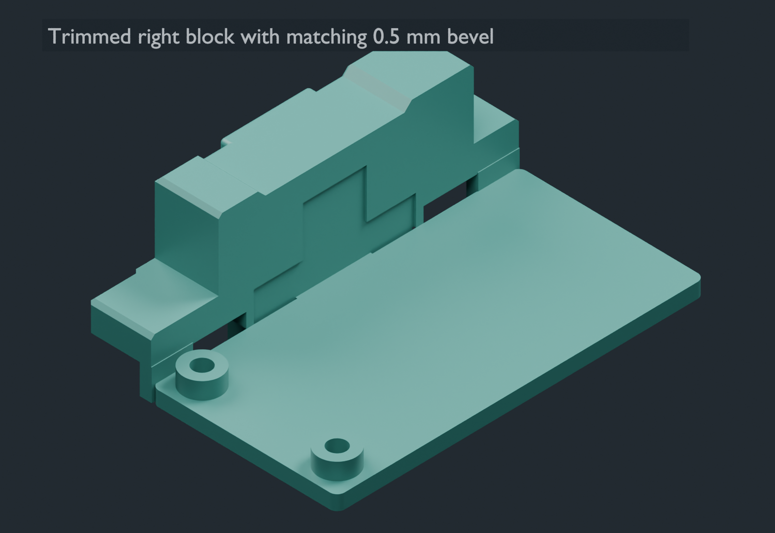
hardware/LaunchLab_v040_right_block_print/renders/03_bare_mount.png
