shadohead/launchlab-mini/hardware/M5_level_support_v044/renders/01_assembled.png

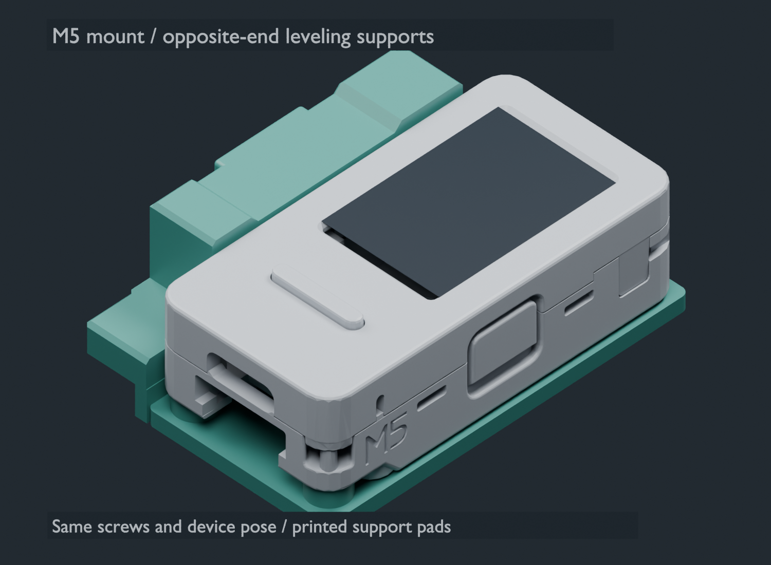
hardware/M5_level_support_v044/renders/01_assembled.png
