shadohead/launchlab-mini/hardware/minimal_TCRT_sensor_only_v042/renders/01_assembled.png

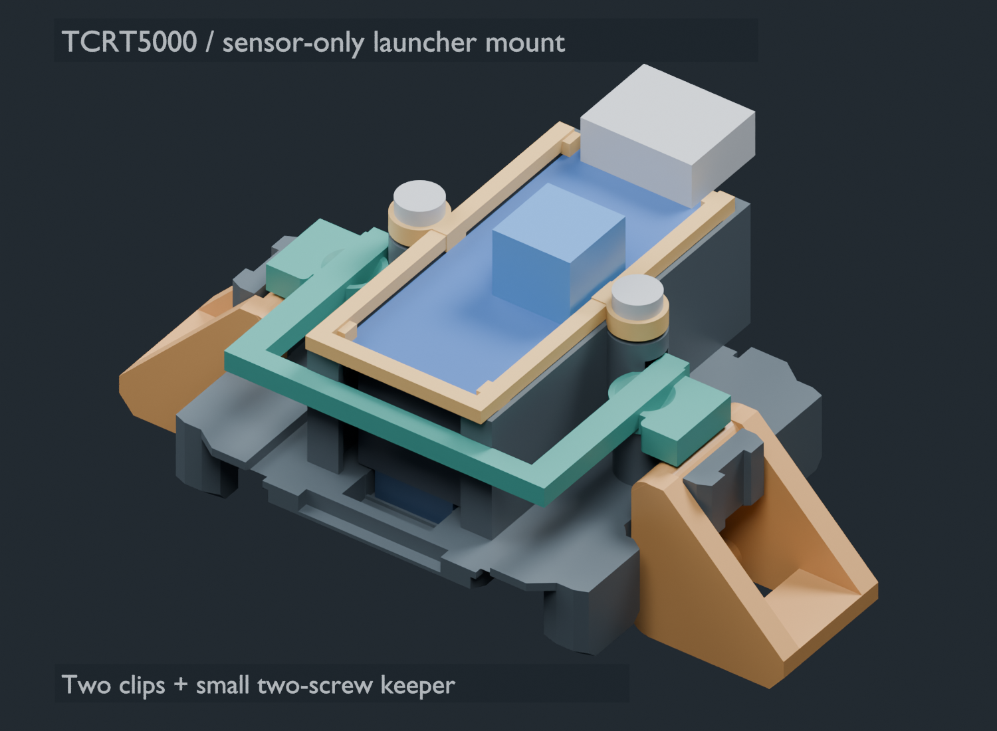
hardware/minimal_TCRT_sensor_only_v042/renders/01_assembled.png
