shadohead/launchlab-mini/hardware/minimal_TCRT_split_keepers_v043/renders/01_assembled.png

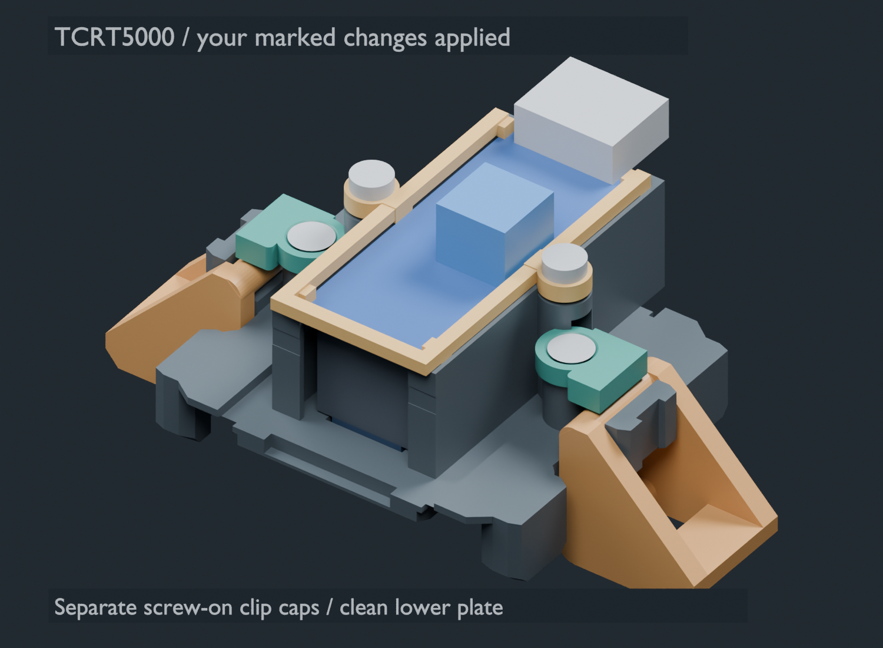
hardware/minimal_TCRT_split_keepers_v043/renders/01_assembled.png
