shadohead/launchlab-mini/hardware/minimal_TCRT_stack_v041/renders/01_assembled.png

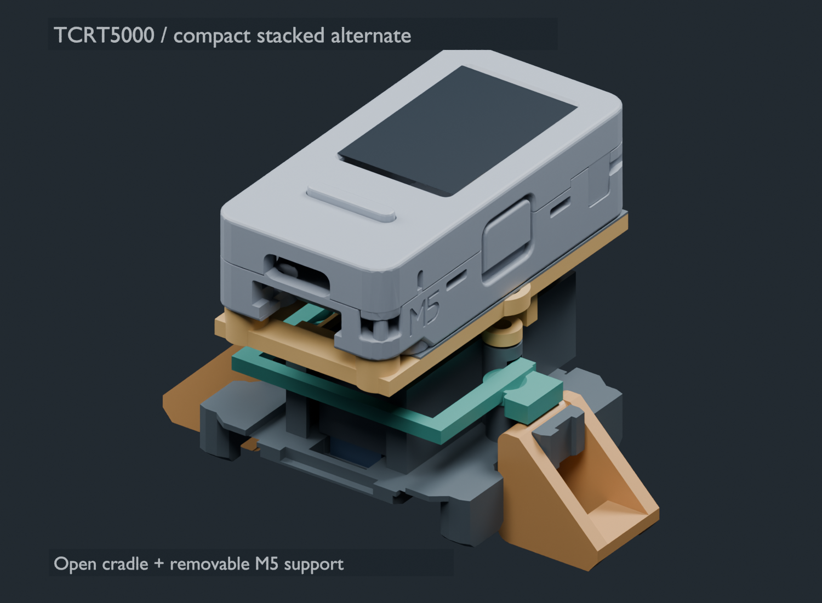
hardware/minimal_TCRT_stack_v041/renders/01_assembled.png
