shadohead/launchlab-mini/firmware/releases/0.11.2-sticks3-qre1113-scorepreview/source/power_status.h

#pragma once
#include <algorithm>
#include <cstdint>

class InactivityTimer {
public:
  static constexpr uint8_t DEFAULT_MINUTES=3;
  static bool validMinutes(uint8_t minutes) {
    return minutes>=1 && minutes<=10;
  }
  static uint8_t nextMinutes(uint8_t minutes) {
    return validMinutes(minutes) && minutes<10 ? minutes+1 : 1;
  }
  bool setMinutes(uint8_t minutes) {
    if(!validMinutes(minutes))return false;
    minutes_=minutes;return true;
  }
  uint8_t minutes()const{return minutes_;}
  uint32_t timeout()const{return uint32_t(minutes_)*60*1000;}
  void touch(uint32_t now){lastActivity_=now;}
  uint32_t elapsed(uint32_t now)const{return now-lastActivity_;}
  uint32_t remaining(uint32_t now)const {
    const uint32_t idle=elapsed(now);return idle>=timeout()?0:timeout()-idle;
  }
  bool due(uint32_t now,bool measuring=false)const{return !measuring && elapsed(now)>=timeout();}
private:
  uint32_t lastActivity_=0;
  uint8_t minutes_=DEFAULT_MINUTES;
};

struct StickS3Battery {
  static constexpr uint32_t STALE_MS=15000;
  uint16_t millivolts=0;
  int percent=-1;
  bool voltageOk=false,chargeKnown=false,charging=false;
  uint32_t sampledAt=0;
  void update(uint16_t mv,bool voltageRead,bool chargeRead,uint8_t gpioBits,uint32_t now) {
    sampledAt=now;millivolts=mv;
    voltageOk=voltageRead && mv>=2500 && mv<=4350;
    // Match M5Unified 0.2.23's voltage-based estimate, using the one checked
    // PM1 read. This is approximate charge, not a measured runtime remaining.
    percent=voltageOk?std::max(0,std::min(100,(int(mv)-3300)*100/800)):-1;
    chargeKnown=chargeRead;charging=chargeRead && !(gpioBits&1); // PM1 G0 active low.
  }
  bool valid(uint32_t now)const{return voltageOk && now-sampledAt<=STALE_MS;}
  const char *chargeName()const{return !chargeKnown?"unknown":charging?"charging":"not_charging";}
};
