shadohead/launchlab-mini/firmware/releases/0.11.2-sticks3-qre1113-scorepreview/tests/test_motion_playback.cpp

// Host regression for the actual .ino feedback call and redraw predicate.
// check_motion_playback.py extracts those two blocks verbatim at test time.
#include <algorithm>
#include <cassert>
#include <cmath>
#include <cstdint>
#include <cstdio>
#include <iostream>
#include <memory>
#include <vector>
static constexpr uint16_t TFT_BLACK=0,TFT_WHITE=0xffff,TFT_DARKGREY=0x7bef,TFT_CYAN=0x07ff,TFT_ORANGE=0xfd20;
static constexpr int top_center=0,top_right=1;
namespace fonts {static int Font4=4;}
namespace lgfx {
class LGFXBase {
public:
  std::vector<int> primitives;
  std::vector<int> triangles,usbLines;
  std::vector<std::pair<int,int>> bubbles;
  int width()const{return 135;}
  void setTextDatum(int){} void setTextColor(uint16_t,uint16_t){}
  int textWidth(const char *s,const int*)const{unsigned n=0;while(s[n])++n;return int(n)*13;}
  void drawString(const char*,int,int,int){}
  void drawLine(int a,int b,int c,int d,uint16_t ink){append({1,a,b,c,d,ink});if(ink==TFT_WHITE)usbLines.insert(usbLines.end(),{a,b,c,d});}
  void drawFastHLine(int a,int b,int c,uint16_t ink){drawLine(a,b,a+c-1,b,ink);}
  void drawFastVLine(int a,int b,int c,uint16_t ink){drawLine(a,b,a,b+c-1,ink);}
  void drawRect(int a,int b,int c,int d,uint16_t ink){append({2,a,b,c,d,ink});}
  void drawCircle(int a,int b,int c,uint16_t ink){append({3,a,b,c,ink});}
  void fillCircle(int a,int b,int c,uint16_t ink){append({4,a,b,c,ink});if(c==4)bubbles.emplace_back(a,b);}
  void fillTriangle(int a,int b,int c,int d,int e,int f,uint16_t ink){append({5,a,b,c,d,e,f,ink});triangles.insert(triangles.end(),{a,b,c,d,e,f,ink});}
private:
  void append(std::initializer_list<int> values){primitives.insert(primitives.end(),values);}
};
}
#include "../LaunchLabMini/motion_ui.h"
#include "../LaunchLabMini/appearance.h"
static Appearance::Celebration bestEffect;static uint16_t themeAccent(){return Appearance::accent(Appearance::Theme::Classic);}
#include "../LaunchLabMini/launch_feedback.h"
#include "fixtures/tilt_launch96.h"
static uint32_t hostNow=0;
static uint32_t millis(){return hostNow;}
static LaunchFeedback launchFeedback;
static LaunchMotion::Trace latestMotion,referenceMotion,demoMotion,demoReference;
struct PracticeFake {}practice;
struct StoreFake {bool pending(const PracticeFake&)const{return false;}}practiceStore;
static bool motionPending=false,motionDemo=false,tournamentMode=false,diagnostics=false,historyPage=false,screenReady=true;
static bool displayFlipped=false;
static bool visibleDisplayFlipped(){return displayFlipped;}
#include "motion_playback_wiring.h"
static unsigned failures=0,frames=0;
static void require(bool ok,const char *message) {
  if(!ok){if(failures<12)std::cerr<<"FAIL: "<<message<<'\n';++failures;}
}
static LaunchMotion::Trace capture(uint32_t durationMs) {
  auto ring=std::make_unique<LaunchMotion::Ring>();
  const uint64_t start=2000000,end=start+durationMs*1000;
  for(uint64_t us=start-500000;us<=end+260000;us+=10000) {
    LaunchMotion::Sample s;s.us=us;s.fused=s.settled=true;s.a[2]=1;
    const float rate[3]={0,45,0};s.q.integrate(rate,float(us-(start-500000))*.000001f);
    ring->feed(s);
  }
  auto t=ring->build(start,end,6000,7);
  require(t.valid() && t.fused && t.durationMs==durationMs,"recorded optical duration retained");
  return t;
}
static void checkFrame(uint32_t elapsed) {
  lgfx::LGFXBase actual,expected;
  const auto sampledElapsed=drawActualFeedback(actual);
  // At elapsed E, display the recorded pose E ms after context start. This
  // oracle uses the existing normalized renderer, independently of the new
  // clock helper and regardless of how many frames were rendered before it.
  const uint32_t span=latestMotion.points[latestMotion.count-1].ms-latestMotion.points[0].ms;
  const float progress=std::min(elapsed,span)/float(span);
  drawExpectedFeedback(expected,progress);
  require(actual.primitives==expected.primitives,"rendered pose/progress must use recording milliseconds, not fixed recap duration");
  finishActualFeedbackFrame(sampledElapsed);
  ++frames;
}
static void schedule(const LaunchMotion::Trace &t,const std::vector<uint32_t> &intervals,uint32_t start=10000) {
  latestMotion=t;launchFeedback.show(start);hostNow=start;checkFrame(0);
  uint32_t lastDraw=start,elapsed=0;unsigned index=0;
  const uint32_t span=t.points[t.count-1].ms-t.points[0].ms;
  bool endpointDisplayed=false;uint32_t endpointAt=0;
  while(elapsed<span+1000) {
    elapsed+=intervals[index++%intervals.size()];hostNow=start+elapsed;
    if(actualNeedsReplayFrame(hostNow,lastDraw)) {
      checkFrame(elapsed);lastDraw=hostNow;
      if(elapsed>=span && !endpointDisplayed){endpointDisplayed=true;endpointAt=elapsed;}
    }
  }
  require(endpointDisplayed,"redraw scheduler must present endpoint, including a stalled frame that crosses the end");
  const auto longestInterval=*std::max_element(intervals.begin(),intervals.end());
  require(endpointAt<span+50+longestInterval,"visible endpoint latency must be bounded by redraw cadence, not a fixed replay duration");
  require(!actualNeedsReplayFrame(hostNow,lastDraw),"redraw scheduler must stop after the recording endpoint is displayed");
  hostNow=start+span;checkFrame(span);
  hostNow=start+span+1000;checkFrame(span+1000);
}
int main() {
  LaunchMotion::Trace dots;MotionUI::makeDemo(dots,false);
  dots.startLevel={StickS3Level::State::Valid,30,.6f,.8f};
  dots.endLevel={StickS3Level::State::Valid,30,-.8f,.6f};
  lgfx::LGFXBase normal,flipped;
  MotionUI::feedback(normal,dots,false,false,1,false);
  MotionUI::feedback(flipped,dots,false,false,1,true);
  require(normal.bubbles==std::vector<std::pair<int,int>>{{44,221},{89,219}},"native frozen Start/End dots");
  require(flipped.bubbles==std::vector<std::pair<int,int>>{{28,201},{109,203}},"180-degree frozen Start/End dots");
  require(dots.startLevel.right==.6f && dots.endLevel.down==.6f,"display orientation cannot change the stored launch");
  // Independent display-frame oracle: change every recorded board sample to
  // the screen's upside-down axes before the existing heading normalization.
  // This must match applying the setting to a cached native replay at draw time.
  auto displayAxes=dots;
  for(auto &p:displayAxes.points) {
    const auto old=p;
    p.q[0]=-old.q[3];p.q[1]=old.q[2];p.q[2]=-old.q[1];p.q[3]=old.q[0];
  }
  for(float progress:{.31f,.51f,.74f,.92f}) {
    lgfx::LGFXBase native,inverted,oracle,restored;
    MotionUI::feedback(oracle,displayAxes,false,false,progress,false);
    MotionUI::feedback(native,dots,false,false,progress,false);
    MotionUI::feedback(inverted,dots,false,false,progress,true);
    require(!inverted.triangles.empty() && inverted.triangles==oracle.triangles,"flipped 3D body must follow the display axes, including cached replay");
    require((inverted.triangles!=native.triangles)==(progress>.4f),"asymmetric tilt must change direction after display flip while neutral stays aligned");
    require(inverted.usbLines!=oracle.usbLines,"USB marker must stay on the physical USB end, not the logical screen bottom");
    MotionUI::feedback(restored,dots,false,false,progress,false);
    require(restored.primitives==native.primitives,"returning to native orientation must restore the same cached frame");
  }
  // Both RPM estimators feed the same trace/recap consumer; RPM selection must
  // not alter its clock. Durations bracket short real pulls and the 2500 ms cap.
  for(uint32_t duration:{1u,78u,83u,88u,400u,450u,1250u,1800u,2500u}) {
    auto t=capture(duration);
    for(const auto &intervals:std::vector<std::vector<uint32_t>>{{16},{33},{50},{100},{7,43,120,5,60,200},{50,700,50,50}})
      schedule(t,intervals);
    t.rpm=5900;schedule(t,{50});
  }
  const auto saved=savedTiltLaunch96();
  for(const auto &intervals:std::vector<std::vector<uint32_t>>{{16},{50},{100},{7,43,120,5,60,200}})schedule(saved,intervals);
  latestMotion=capture(400);launchFeedback.show(10000);hostNow=10200;checkFrame(0);
  // The actual firmware restarts show() after post-roll capture becomes ready.
  launchFeedback.show(10300);hostNow=10300;checkFrame(0);hostNow=10500;checkFrame(200);
  launchFeedback.toggle(10501,true);launchFeedback.toggle(11000,true);hostNow=11000;checkFrame(0);
  // The five-second recap still holds the endpoint after real-time animation.
  require(!launchFeedback.tick(15999) && launchFeedback.tick(16000),"five-second recap expiry retained");
  schedule(saved,{50},UINT32_MAX-30);
  latestMotion=saved;launchFeedback.show(10000);hostNow=10000;motionPending=true;
  require(!actualNeedsReplayFrame(10060,10000),"pending capture must not animate");motionPending=false;
  std::cout<<(failures?"FAIL":"PASS")<<": "<<frames<<" actual firmware-rendered frames; recorded/replay duration across 16/33/50/100 ms, jitter, 700 ms stall, saved 83 ms pull, bounded visible endpoint latency, capture restart, manual reopen, five-second hold, timer wrap; failures="<<failures<<'\n';
  return failures?1:0;
}
