shadohead/launchlab-mini/firmware/releases/0.11.2-sticks3-qre1113-scorepreview/tests/test_controls.cpp

#include "controls.h"
#include <cassert>
#include <iostream>
using namespace Controls;
int main() {
  State s;assert(s.autoRecap() && s.tapA()==Effect::Recap);
  assert(s.holdB(true)==Effect::Recap && s.holdB()==Effect::None);
  s.tapB();assert(s.page==Page::Menu && s.menu==0 && !s.autoRecap());
  s.tapA();assert(s.page==Page::HistoryMenu);
  for(unsigned view=0;view<3;++view) {
    s.history=view;s.tapA();assert(s.page==Page::History && s.tapB()==Effect::Older);
    s.holdB();assert(s.page==Page::HistoryMenu && s.history==view);
  }
  s.history=3;s.tapA();assert(s.page==Page::Menu);
  s.menu=1;s.tapA();assert(s.page==Page::NewSession && !s.startSession);
  assert(s.tapA()==Effect::None && s.page==Page::Menu);
  s.tapA();s.tapB();assert(s.tapA()==Effect::NewSession && s.page==Page::Menu);
  s.menu=3;s.tapA();assert(s.page==Page::Settings);
  for(unsigned row=0;row<SETTING_COUNT;++row) {
    s.setting=row;assert(s.tapA()==Effect::BeginEdit && s.page==Page::Edit);
    assert(s.tapA()==Effect::Apply && s.page==Page::Edit); // Backend must confirm success.
    assert(s.holdA()==Effect::None);assert(s.holdB()==Effect::CancelEdit && s.page==Page::Settings);
  }
  s.setting=SETTING_COUNT;s.tapA();assert(s.page==Page::Menu);
  s.holdB();assert(s.page==Page::Main);
  assert(s.holdA(true)==Effect::None && s.page==Page::Main);
  assert(s.holdA()==Effect::Tournament && s.page==Page::Tournament && !s.autoRecap());
  assert(s.tapA()==Effect::None && s.holdB()==Effect::None && s.page==Page::Tournament);
  assert(s.tapB()==Effect::Tournament && s.page==Page::Tournament);
  assert(s.holdA()==Effect::Tournament && s.page==Page::Main);
  for(unsigned row=0;row<SETTING_COUNT;++row) {
    s.page=Page::Edit;s.setting=row;s.draft=row==0?3:row==2?40:0;
    const unsigned original=s.draft,cycle=row==0 || row==2?10:row==5?4:row==6?6:2;
    for(unsigned i=0;i<cycle;++i)assert(s.tapB()==Effect::Preview);
    assert(s.draft==original);
  }
  // Hold/release must never execute both actions, including a synthetic
  // library release click and a new short press immediately afterwards.
  Gesture gesture;assert(!gesture.click(true,false,false));
  assert(gesture.click(false,false,true));
  assert(!gesture.click(true,false,false));assert(!gesture.click(false,true,false));
  assert(!gesture.click(false,false,true));assert(!gesture.click(true,false,false));
  assert(gesture.click(false,false,true));
  for(unsigned page=0;page<=unsigned(Page::Tournament);++page)
    for(unsigned menu=0;menu<6;++menu)for(unsigned setting=0;setting<=SETTING_COUNT;++setting)for(uint8_t view=0;view<2;++view) {
      State before;before.page=Page(page);before.menu=menu;before.setting=setting;before.history=2;
      State after;uint8_t saved=99;
      assert(decodeWake(encodeWake(before,view),after,saved));
      assert(after.page==(before.page==Page::Edit?Page::Settings:before.page));
      assert(after.menu==menu && after.setting==setting && after.history==2 && saved==view);
    }
  State out;uint8_t view=0;
  assert(decodeWake(LEGACY_WAKE_MAGIC|uint32_t(Page::Settings)|(5u<<9),out,view) && out.setting==SETTING_COUNT);
  for(uint32_t corrupt:{0u,WAKE_MAGIC|15u,WAKE_MAGIC|uint32_t(Page::Edit),WAKE_MAGIC|(7u<<4),LEGACY_WAKE_MAGIC|(7u<<9),WAKE_MAGIC|0x2000u})
    assert(!decodeWake(corrupt,out,view));
  std::cout<<"PASS: consistent actions, visible menu/back, deliberate sessions, staged settings, tournament lock, hold release, wake round trips and corruption\n";
}
