shadohead/launchlab-mini/firmware/releases/0.11.2-sticks3-qre1113-scorepreview/tests/test_display_flip.cpp

#include "../LaunchLabMini/display_flip_setting.h"
#include <cassert>
#include <iostream>

int main() {
  Preferences prefs;prefs.begin("launchlab-mini",false);
  const uint8_t prior[]={4,8,15,16,23,42};
  for(const char *key:{"sleep_min","bright_pct","rpm_method","wake_ui","history0","reference0"})
    prefs.putBytes(key,prior,sizeof(prior));
  const auto existing=Preferences::data;
  bool flipped=true;
  assert(DisplayFlipSetting::load(prefs,flipped) && !flipped);
  assert(Preferences::data==existing);
  for(bool selected:{true,false,true}) {
    assert(DisplayFlipSetting::save(prefs,selected));
    Preferences reboot;reboot.begin("launchlab-mini",false);
    assert(DisplayFlipSetting::load(reboot,flipped) && flipped==selected);
    for(const auto &entry:existing)assert(Preferences::data.at(entry.first)==entry.second);
  }
  const auto good=Preferences::data;
  Preferences::failWrite=true;
  assert(!DisplayFlipSetting::save(prefs,false) && Preferences::data==good);
  Preferences::failWrite=false;Preferences::shortRead=true;
  assert(!DisplayFlipSetting::load(prefs,flipped) && !flipped);
  assert(Preferences::data==good);
  Preferences::shortRead=false;
  auto &record=Preferences::data[std::string("launchlab-mini")+DisplayFlipSetting::KEY];
  record[2]=2;
  const auto corrupt=Preferences::data;
  assert(!DisplayFlipSetting::load(prefs,flipped) && !flipped && Preferences::data==corrupt);
  Preferences::zeroLengthKeys.insert(std::string("launchlab-mini")+DisplayFlipSetting::KEY);
  assert(!DisplayFlipSetting::load(prefs,flipped) && !flipped && Preferences::data==corrupt);
  std::cout<<"PASS: normal default without writes, flip survives restart, other settings/history retained, failed writes and invalid reads retained safely\n";
}
