shadohead/launchlab-mini/firmware/releases/0.11.2-sticks3-qre1113-scorepreview/tests/test_sticks3_power.cpp

#include "../LaunchLabMini/power_status.h"
#include <cassert>
#include <iostream>

int main() {
  InactivityTimer timer;timer.touch(1000);
  assert(timer.minutes()==3 && timer.timeout()==180000);
  assert(timer.remaining(1000)==180000 && !timer.due(180999));
  assert(timer.due(181000) && timer.remaining(181000)==0);
  assert(!timer.due(181000,true)); // active measured burst is protected
  for(uint8_t minutes=1;minutes<=10;++minutes) {
    assert(timer.setMinutes(minutes));timer.touch(1000);
    assert(!timer.due(1000+timer.timeout()-1));assert(timer.due(1000+timer.timeout()));
    timer.touch(1000+timer.timeout());assert(timer.remaining(1000+timer.timeout())==timer.timeout());
    timer.touch(UINT32_MAX-50000);
    assert(!timer.due(uint32_t(UINT32_MAX-50000+timer.timeout()-1)));
    assert(timer.due(uint32_t(UINT32_MAX-50000+timer.timeout())));
  }
  for(uint8_t bad:{0,11,15,30,255})assert(!timer.setMinutes(bad) && timer.minutes()==10);
  uint8_t minutes=1;for(unsigned i=0;i<10;++i)minutes=InactivityTimer::nextMinutes(minutes);
  assert(minutes==1);

  StickS3Battery b;
  assert(!b.valid(0) && b.percent==-1);
  b.update(3700,true,true,0,100);assert(b.valid(100) && b.percent==50 && b.charging);
  assert(b.valid(15100) && !b.valid(15101));
  b.update(4200,true,true,1,200);assert(b.percent==100 && !b.charging);
  b.update(3000,true,true,1,200);assert(b.percent==0);
  for(unsigned mv:{0u,2400u,4400u,65535u}) {
    b.update(mv,true,true,0,300);assert(!b.valid(300) && b.percent==-1);
  }
  b.update(3700,false,false,0,400);assert(!b.valid(400) && !b.chargeKnown && !b.charging);
  b.update(3900,true,false,0,500);assert(b.valid(500) && b.percent==75 && !b.chargeKnown);
  b.update(3900,true,true,1,UINT32_MAX-1000);assert(b.valid(1000));
  std::cout<<"PASS: 3-minute default, all 1–10 minute timeouts, invalid-value rejection, activity reset, active-burst guard, millis wrap, checked battery voltage, estimate limits, stale/error handling and charging GPIO\n";
}
